exsilium/pxbee-trigger/pxbee/headers/radio_gpios.h

/****************************************************************************
 * Copyright (C) 2012 - 2015 Digi International Inc, All Rights Reserved.
 *
 * This software is provided as instructional material without charge 
 * by Digi International for use by its employees and customers
 * subject to the following terms.
 *
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
 * LIABILITY
 * IN NO EVENT SHALL DIGI INTERNATIONAL BE LIABLE FOR ANY CLAIM, DAMAGES, 
 * OR OTHER LIABILITY, WHETHER IN AN ACTION OF CONTRACT, TORT, OR OTHERWISE, 
 * ARISING FROM, OUT OF, OR IN CONNECTION WITH THE SOFTWARE, OR THE USE 
 * OR OTHER DEALINGS WITH THE SOFTWARE.
 *
 ****************************************************************************/
#ifndef __RADIO_GPIO_H_
#define __RADIO_GPIO_H_

#include <xbee_config.h>

/* Pull-Direction and Pull-Resistor bit shifting for each XPIN according to
 * Datasheet */
#ifdef CONFIG_XBEE_THT

#define shift_xpin_4  (1<<10)
#define shift_xpin_6  (1<<11)
#define shift_xpin_7  (1<<12)
#define shift_xpin_9  (1<<6)
#define shift_xpin_11 (1<<0)
#define shift_xpin_13 (1<<9)
#define shift_xpin_15 (1<<8)
#define shift_xpin_17 (1<<1)
#define shift_xpin_18 (1<<2)
#define shift_xpin_19 (1<<3)
#define shift_xpin_20 (1<<4)

#elif defined (CONFIG_XBEE_SMT)
#define shift_xpin_5  (1<<10)
#define shift_xpin_7  (1<<11)
#define shift_xpin_8  (1<<12)
#define shift_xpin_10 (1<<6)
#define shift_xpin_24 (1<<0)
#define shift_xpin_26 (1<<9)
#define shift_xpin_28 (1<<8)
#define shift_xpin_30 (1<<1)
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
#endif
#ifndef orPR32
#define orPR32 0
#endif
#ifndef andPR32
#define andPR32 ~0
#endif

#ifndef orPD33
#define orPD33 0
#endif
#ifndef andPD33
#define andPD33 ~0
#endif
#ifndef orPR33
#define orPR33 0
#endif
#ifndef andPR33
#define andPR33 ~0
#endif

#endif /* __RADIO_GPIO_H_ */
