exsilium/pxbee-trigger/pxbee/headers/mc9s08qe128.h

/* Based on CPU DB MC9S08QE128_80, version 3.00.066 (RegistersPrg V2.32) */
/*
** ###################################################################
**     Filename  : mc9s08qe128.h
**     Processor : MC9S08QE128CLK
**     FileFormat: V2.32
**     DataSheet : MC9S08QE128RM Rev. 2 6/2007
**     Compiler  : CodeWarrior compiler
**     Date/Time : 5.10.2010, 13:55
**     Abstract  :
**         This header implements the mapping of I/O devices.
**
**     Copyright : 1997 - 2010 Freescale Semiconductor, Inc. All Rights Reserved.
**     
**     http      : www.freescale.com
**     mail      : support@freescale.com
**
**     CPU Registers Revisions:
**               - none
**
**     File-Format-Revisions:
**      - 22.01.2007, V2.12 :
**               - Changes have not affected this file (because they are related to another family)
**      - 01.03.2007, V2.13 :
**               - Flash commands constants values converted to HEX format
**      - 02.03.2007, V2.14 :
**               - Interrupt vector numbers added into .H, see VectorNumber_*
**      - 26.03.2007, V2.15 :
**               - Changes have not affected this file (because they are related to another family)
**      - 10.05.2007, V2.16 :
**               - Fixed flash commands definition for ColdFireV1 assembler (equ -> .equ)
**      - 05.06.2007, V2.17 :
**               - Changes have not affected this file (because they are related to another family)
**      - 19.07.2007, V2.18 :
**               - Improved number of blanked lines inside register structures
**      - 06.08.2007, V2.19 :
**               - CPUDB revisions generated ahead of the file-format revisions.
**      - 11.09.2007, V2.20 :
**               - Added comment about initialization of unbonded pins.
**      - 02.01.2008, V2.21 :
**               - Changes have not affected this file (because they are related to another family)
**      - 13.02.2008, V2.22 :
**               - Changes have not affected this file (because they are related to another family)
**      - 20.02.2008, V2.23 :
**               - Changes have not affected this file (because they are related to another family)
**      - 03.07.2008, V2.24 :
**               - Added support for bits with name starting with number (like "1HZ")
**      - 28.11.2008, V2.25 :
**               - StandBy RAM array declaration for ANSI-C added
**      - 1.12.2008, V2.26 :
**               - Duplication of bit (or bit-group) name with register name is not marked as a problem, if register is internal only and it is not displayed in I/O map.
**      - 17.3.2009, V2.27 :
**               - Merged bit-group is not generated, if the name matches with another bit name in the register
**      - 6.4.2009, V2.28 :
**               - Fixed generation of merged bits for bit-groups with a digit at the end, if group-name is defined in CPUDB
**      - 3.8.2009, V2.29 :
**               - If there is just one bits group matching register name, single bits are not generated
**      - 10.9.2009, V2.30 :
**               - Fixed generation of registers arrays.
**      - 15.10.2009, V2.31 :
**               - HCS08 family: Bits and bit-groups are published for 16-bit registers: 8-bit overlay registers are required.
**      - 18.05.2010, V2.32 :
**               - MISRA compliance: U/UL suffixes added to all numbers (_MASK,_BITNUM and addresses)
**
**     Not all general-purpose I/O pins are available on all packages or on all mask sets of a specific
**     derivative device. To avoid extra current drain from floating input pins, the user’s reset
**     initialization routine in the application program must either enable on-chip pull-up devices
**     or change the direction of unconnected pins to outputs so the pins do not float.
** ###################################################################
*/

#ifndef _MC9S08QE128_H
#define _MC9S08QE128_H

#define FOPT_SEC00_MASK                 1U

/*lint -save  -e950 -esym(960,18.4) -e46 -esym(961,19.7) Disable MISRA rule (1.1,18.4,6.4,19.7) checking. */
/* Types definition */
typedef unsigned char byte;
typedef unsigned int word;
typedef unsigned long dword;
typedef unsigned long dlong[2];

/* Watchdog reset macro */
#ifndef __RESET_WATCHDOG
#ifdef _lint
  #define __RESET_WATCHDOG()  /* empty */
#else
  #define __RESET_WATCHDOG() {asm sta SRS;}
#endif
#endif /* __RESET_WATCHDOG */

#define REG_BASE 0x0000                /* Base address for the I/O register block */


#pragma MESSAGE DISABLE C1106 /* WARNING C1106: Non-standard bitfield type */

/**************** interrupt vector numbers ****************/
#define VectorNumber_Vtpm3ovf           31U
#define VectorNumber_Vtpm3ch5           30U
#define VectorNumber_Vtpm3ch4           29U
#define VectorNumber_Vtpm3ch3           28U
#define VectorNumber_Vtpm3ch2           27U
#define VectorNumber_Vtpm3ch1           26U
#define VectorNumber_Vtpm3ch0           25U
#define VectorNumber_Vrtc               24U
#define VectorNumber_Vsci2tx            23U
#define VectorNumber_Vsci2rx            22U
#define VectorNumber_Vsci2err           21U
#define VectorNumber_Vacmpx             20U
#define VectorNumber_Vadc               19U
#define VectorNumber_Vkeyboard          18U
#define VectorNumber_Viicx              17U
#define VectorNumber_Vsci1tx            16U
#define VectorNumber_Vsci1rx            15U
#define VectorNumber_Vsci1err           14U
#define VectorNumber_Vspi1              13U
#define VectorNumber_Vspi2              12U
#define VectorNumber_Vtpm2ovf           11U
#define VectorNumber_Vtpm2ch2           10U
#define VectorNumber_Vtpm2ch1           9U
#define VectorNumber_Vtpm2ch0           8U
#define VectorNumber_Vtpm1ovf           7U
#define VectorNumber_Vtpm1ch2           6U
#define VectorNumber_Vtpm1ch1           5U
#define VectorNumber_Vtpm1ch0           4U
#define VectorNumber_Vlvd               3U
#define VectorNumber_Virq               2U
#define VectorNumber_Vswi               1U
#define VectorNumber_Vreset             0U

/**************** interrupt vector table ****************/
#define Vtpm3ovf                        0xFFC0U
#define Vtpm3ch5                        0xFFC2U
#define Vtpm3ch4                        0xFFC4U
#define Vtpm3ch3                        0xFFC6U
#define Vtpm3ch2                        0xFFC8U
#define Vtpm3ch1                        0xFFCAU
#define Vtpm3ch0                        0xFFCCU
#define Vrtc                            0xFFCEU
#define Vsci2tx                         0xFFD0U
#define Vsci2rx                         0xFFD2U
#define Vsci2err                        0xFFD4U
#define Vacmpx                          0xFFD6U
#define Vadc                            0xFFD8U
#define Vkeyboard                       0xFFDAU
#define Viicx                           0xFFDCU
#define Vsci1tx                         0xFFDEU
#define Vsci1rx                         0xFFE0U
#define Vsci1err                        0xFFE2U
#define Vspi1                           0xFFE4U
#define Vspi2                           0xFFE6U
#define Vtpm2ovf                        0xFFE8U
#define Vtpm2ch2                        0xFFEAU
#define Vtpm2ch1                        0xFFECU
#define Vtpm2ch0                        0xFFEEU
#define Vtpm1ovf                        0xFFF0U
#define Vtpm1ch2                        0xFFF2U
#define Vtpm1ch1                        0xFFF4U
#define Vtpm1ch0                        0xFFF6U
#define Vlvd                            0xFFF8U
#define Virq                            0xFFFAU
#define Vswi                            0xFFFCU
#define Vreset                          0xFFFEU

/**************** registers I/O map ****************/

/*** PTAD - Port A Data Register; 0x00000000 ***/
typedef union {
  byte Byte;
  struct {
    byte PTAD0       :1;                                       /* Port A Data Register Bit 0 */
    byte PTAD1       :1;                                       /* Port A Data Register Bit 1 */
    byte PTAD2       :1;                                       /* Port A Data Register Bit 2 */
    byte PTAD3       :1;                                       /* Port A Data Register Bit 3 */
    byte PTAD4       :1;                                       /* Port A Data Register Bit 4 */
    byte PTAD5       :1;                                       /* Port A Data Register Bit 5 */
    byte PTAD6       :1;                                       /* Port A Data Register Bit 6 */
    byte PTAD7       :1;                                       /* Port A Data Register Bit 7 */
  } Bits;
} PTADSTR;
extern volatile PTADSTR _PTAD @0x00000000;
#define PTAD                            _PTAD.Byte
#define PTAD_PTAD0                      _PTAD.Bits.PTAD0
#define PTAD_PTAD1                      _PTAD.Bits.PTAD1
#define PTAD_PTAD2                      _PTAD.Bits.PTAD2
#define PTAD_PTAD3                      _PTAD.Bits.PTAD3
#define PTAD_PTAD4                      _PTAD.Bits.PTAD4
#define PTAD_PTAD5                      _PTAD.Bits.PTAD5
#define PTAD_PTAD6                      _PTAD.Bits.PTAD6
#define PTAD_PTAD7                      _PTAD.Bits.PTAD7

#define PTAD_PTAD0_MASK                 1U
#define PTAD_PTAD1_MASK                 2U
#define PTAD_PTAD2_MASK                 4U
#define PTAD_PTAD3_MASK                 8U
#define PTAD_PTAD4_MASK                 16U
#define PTAD_PTAD5_MASK                 32U
#define PTAD_PTAD6_MASK                 64U
#define PTAD_PTAD7_MASK                 128U


/*** PTADD - Port A Data Direction Register; 0x00000001 ***/
typedef union {
  byte Byte;
  struct {
    byte PTADD0      :1;                                       /* Data Direction for Port A Bit 0 */
    byte PTADD1      :1;                                       /* Data Direction for Port A Bit 1 */
    byte PTADD2      :1;                                       /* Data Direction for Port A Bit 2 */
    byte PTADD3      :1;                                       /* Data Direction for Port A Bit 3 */
    byte PTADD4      :1;                                       /* Data Direction for Port A Bit 4 */
    byte PTADD5      :1;                                       /* Data Direction for Port A Bit 5 */
    byte PTADD6      :1;                                       /* Data Direction for Port A Bit 6 */
    byte PTADD7      :1;                                       /* Data Direction for Port A Bit 7 */
  } Bits;
} PTADDSTR;
extern volatile PTADDSTR _PTADD @0x00000001;
#define PTADD                           _PTADD.Byte
#define PTADD_PTADD0                    _PTADD.Bits.PTADD0
#define PTADD_PTADD1                    _PTADD.Bits.PTADD1
#define PTADD_PTADD2                    _PTADD.Bits.PTADD2
#define PTADD_PTADD3                    _PTADD.Bits.PTADD3
#define PTADD_PTADD4                    _PTADD.Bits.PTADD4
#define PTADD_PTADD5                    _PTADD.Bits.PTADD5
#define PTADD_PTADD6                    _PTADD.Bits.PTADD6
#define PTADD_PTADD7                    _PTADD.Bits.PTADD7

#define PTADD_PTADD0_MASK               1U
#define PTADD_PTADD1_MASK               2U
#define PTADD_PTADD2_MASK               4U
#define PTADD_PTADD3_MASK               8U
#define PTADD_PTADD4_MASK               16U
#define PTADD_PTADD5_MASK               32U
#define PTADD_PTADD6_MASK               64U
#define PTADD_PTADD7_MASK               128U


/*** PTBD - Port B Data Register; 0x00000002 ***/
typedef union {
  byte Byte;
  struct {
    byte PTBD0       :1;                                       /* Port B Data Register Bit 0 */
    byte PTBD1       :1;                                       /* Port B Data Register Bit 1 */
    byte PTBD2       :1;                                       /* Port B Data Register Bit 2 */
    byte PTBD3       :1;                                       /* Port B Data Register Bit 3 */
    byte PTBD4       :1;                                       /* Port B Data Register Bit 4 */
    byte PTBD5       :1;                                       /* Port B Data Register Bit 5 */
    byte PTBD6       :1;                                       /* Port B Data Register Bit 6 */
    byte PTBD7       :1;                                       /* Port B Data Register Bit 7 */
  } Bits;
} PTBDSTR;
extern volatile PTBDSTR _PTBD @0x00000002;
#define PTBD                            _PTBD.Byte
#define PTBD_PTBD0                      _PTBD.Bits.PTBD0
#define PTBD_PTBD1                      _PTBD.Bits.PTBD1
#define PTBD_PTBD2                      _PTBD.Bits.PTBD2
#define PTBD_PTBD3                      _PTBD.Bits.PTBD3
#define PTBD_PTBD4                      _PTBD.Bits.PTBD4
#define PTBD_PTBD5                      _PTBD.Bits.PTBD5
#define PTBD_PTBD6                      _PTBD.Bits.PTBD6
#define PTBD_PTBD7                      _PTBD.Bits.PTBD7

#define PTBD_PTBD0_MASK                 1U
#define PTBD_PTBD1_MASK                 2U
#define PTBD_PTBD2_MASK                 4U
#define PTBD_PTBD3_MASK                 8U
#define PTBD_PTBD4_MASK                 16U
#define PTBD_PTBD5_MASK                 32U
#define PTBD_PTBD6_MASK                 64U
#define PTBD_PTBD7_MASK                 128U


/*** PTBDD - Port B Data Direction Register; 0x00000003 ***/
typedef union {
  byte Byte;
  struct {
    byte PTBDD0      :1;                                       /* Data Direction for Port B Bit 0 */
    byte PTBDD1      :1;                                       /* Data Direction for Port B Bit 1 */
    byte PTBDD2      :1;                                       /* Data Direction for Port B Bit 2 */
    byte PTBDD3      :1;                                       /* Data Direction for Port B Bit 3 */
    byte PTBDD4      :1;                                       /* Data Direction for Port B Bit 4 */
    byte PTBDD5      :1;                                       /* Data Direction for Port B Bit 5 */
    byte PTBDD6      :1;                                       /* Data Direction for Port B Bit 6 */
    byte PTBDD7      :1;                                       /* Data Direction for Port B Bit 7 */
  } Bits;
} PTBDDSTR;
extern volatile PTBDDSTR _PTBDD @0x00000003;
#define PTBDD                           _PTBDD.Byte
#define PTBDD_PTBDD0                    _PTBDD.Bits.PTBDD0
#define PTBDD_PTBDD1                    _PTBDD.Bits.PTBDD1
#define PTBDD_PTBDD2                    _PTBDD.Bits.PTBDD2
#define PTBDD_PTBDD3                    _PTBDD.Bits.PTBDD3
#define PTBDD_PTBDD4                    _PTBDD.Bits.PTBDD4
#define PTBDD_PTBDD5                    _PTBDD.Bits.PTBDD5
#define PTBDD_PTBDD6                    _PTBDD.Bits.PTBDD6
#define PTBDD_PTBDD7                    _PTBDD.Bits.PTBDD7

#define PTBDD_PTBDD0_MASK               1U
#define PTBDD_PTBDD1_MASK               2U
#define PTBDD_PTBDD2_MASK               4U
#define PTBDD_PTBDD3_MASK               8U
#define PTBDD_PTBDD4_MASK               16U
#define PTBDD_PTBDD5_MASK               32U
#define PTBDD_PTBDD6_MASK               64U
#define PTBDD_PTBDD7_MASK               128U


/*** PTCD - Port C Data Register; 0x00000004 ***/
typedef union {
  byte Byte;
  struct {
    byte PTCD0       :1;                                       /* Port C Data Register Bit 0 */
    byte PTCD1       :1;                                       /* Port C Data Register Bit 1 */
    byte PTCD2       :1;                                       /* Port C Data Register Bit 2 */
    byte PTCD3       :1;                                       /* Port C Data Register Bit 3 */
    byte PTCD4       :1;                                       /* Port C Data Register Bit 4 */
    byte PTCD5       :1;                                       /* Port C Data Register Bit 5 */
    byte PTCD6       :1;                                       /* Port C Data Register Bit 6 */
    byte PTCD7       :1;                                       /* Port C Data Register Bit 7 */
  } Bits;
} PTCDSTR;
extern volatile PTCDSTR _PTCD @0x00000004;
#define PTCD                            _PTCD.Byte
#define PTCD_PTCD0                      _PTCD.Bits.PTCD0
#define PTCD_PTCD1                      _PTCD.Bits.PTCD1
#define PTCD_PTCD2                      _PTCD.Bits.PTCD2
#define PTCD_PTCD3                      _PTCD.Bits.PTCD3
#define PTCD_PTCD4                      _PTCD.Bits.PTCD4
#define PTCD_PTCD5                      _PTCD.Bits.PTCD5
#define PTCD_PTCD6                      _PTCD.Bits.PTCD6
#define PTCD_PTCD7                      _PTCD.Bits.PTCD7

#define PTCD_PTCD0_MASK                 1U
#define PTCD_PTCD1_MASK                 2U
#define PTCD_PTCD2_MASK                 4U
#define PTCD_PTCD3_MASK                 8U
#define PTCD_PTCD4_MASK                 16U
#define PTCD_PTCD5_MASK                 32U
#define PTCD_PTCD6_MASK                 64U
#define PTCD_PTCD7_MASK                 128U


/*** PTCDD - Port C Data Direction Register; 0x00000005 ***/
typedef union {
  byte Byte;
  struct {
    byte PTCDD0      :1;                                       /* Data Direction for Port C Bit 0 */
    byte PTCDD1      :1;                                       /* Data Direction for Port C Bit 1 */
    byte PTCDD2      :1;                                       /* Data Direction for Port C Bit 2 */
    byte PTCDD3      :1;                                       /* Data Direction for Port C Bit 3 */
    byte PTCDD4      :1;                                       /* Data Direction for Port C Bit 4 */
    byte PTCDD5      :1;                                       /* Data Direction for Port C Bit 5 */
    byte PTCDD6      :1;                                       /* Data Direction for Port C Bit 6 */
    byte PTCDD7      :1;                                       /* Data Direction for Port C Bit 7 */
  } Bits;
} PTCDDSTR;
extern volatile PTCDDSTR _PTCDD @0x00000005;
#define PTCDD                           _PTCDD.Byte
#define PTCDD_PTCDD0                    _PTCDD.Bits.PTCDD0
#define PTCDD_PTCDD1                    _PTCDD.Bits.PTCDD1
#define PTCDD_PTCDD2                    _PTCDD.Bits.PTCDD2
#define PTCDD_PTCDD3                    _PTCDD.Bits.PTCDD3
#define PTCDD_PTCDD4                    _PTCDD.Bits.PTCDD4
#define PTCDD_PTCDD5                    _PTCDD.Bits.PTCDD5
#define PTCDD_PTCDD6                    _PTCDD.Bits.PTCDD6
#define PTCDD_PTCDD7                    _PTCDD.Bits.PTCDD7

#define PTCDD_PTCDD0_MASK               1U
#define PTCDD_PTCDD1_MASK               2U
#define PTCDD_PTCDD2_MASK               4U
#define PTCDD_PTCDD3_MASK               8U
#define PTCDD_PTCDD4_MASK               16U
#define PTCDD_PTCDD5_MASK               32U
#define PTCDD_PTCDD6_MASK               64U
#define PTCDD_PTCDD7_MASK               128U


/*** PTDD - Port D Data Register; 0x00000006 ***/
typedef union {
  byte Byte;
  struct {
    byte PTDD0       :1;                                       /* Port D Data Register Bit 0 */
    byte PTDD1       :1;                                       /* Port D Data Register Bit 1 */
    byte PTDD2       :1;                                       /* Port D Data Register Bit 2 */
    byte PTDD3       :1;                                       /* Port D Data Register Bit 3 */
    byte PTDD4       :1;                                       /* Port D Data Register Bit 4 */
    byte PTDD5       :1;                                       /* Port D Data Register Bit 5 */
    byte PTDD6       :1;                                       /* Port D Data Register Bit 6 */
    byte PTDD7       :1;                                       /* Port D Data Register Bit 7 */
  } Bits;
} PTDDSTR;
extern volatile PTDDSTR _PTDD @0x00000006;
#define PTDD                            _PTDD.Byte
#define PTDD_PTDD0                      _PTDD.Bits.PTDD0
#define PTDD_PTDD1                      _PTDD.Bits.PTDD1
#define PTDD_PTDD2                      _PTDD.Bits.PTDD2
#define PTDD_PTDD3                      _PTDD.Bits.PTDD3
#define PTDD_PTDD4                      _PTDD.Bits.PTDD4
#define PTDD_PTDD5                      _PTDD.Bits.PTDD5
#define PTDD_PTDD6                      _PTDD.Bits.PTDD6
#define PTDD_PTDD7                      _PTDD.Bits.PTDD7

#define PTDD_PTDD0_MASK                 1U
#define PTDD_PTDD1_MASK                 2U
#define PTDD_PTDD2_MASK                 4U
#define PTDD_PTDD3_MASK                 8U
#define PTDD_PTDD4_MASK                 16U
#define PTDD_PTDD5_MASK                 32U
#define PTDD_PTDD6_MASK                 64U
#define PTDD_PTDD7_MASK                 128U


/*** PTDDD - Port D Data Direction Register; 0x00000007 ***/
typedef union {
  byte Byte;
  struct {
    byte PTDDD0      :1;                                       /* Data Direction for Port D Bit 0 */
    byte PTDDD1      :1;                                       /* Data Direction for Port D Bit 1 */
    byte PTDDD2      :1;                                       /* Data Direction for Port D Bit 2 */
    byte PTDDD3      :1;                                       /* Data Direction for Port D Bit 3 */
    byte PTDDD4      :1;                                       /* Data Direction for Port D Bit 4 */
    byte PTDDD5      :1;                                       /* Data Direction for Port D Bit 5 */
    byte PTDDD6      :1;                                       /* Data Direction for Port D Bit 6 */
    byte PTDDD7      :1;                                       /* Data Direction for Port D Bit 7 */
  } Bits;
} PTDDDSTR;
extern volatile PTDDDSTR _PTDDD @0x00000007;
#define PTDDD                           _PTDDD.Byte
#define PTDDD_PTDDD0                    _PTDDD.Bits.PTDDD0
#define PTDDD_PTDDD1                    _PTDDD.Bits.PTDDD1
#define PTDDD_PTDDD2                    _PTDDD.Bits.PTDDD2
#define PTDDD_PTDDD3                    _PTDDD.Bits.PTDDD3
#define PTDDD_PTDDD4                    _PTDDD.Bits.PTDDD4
#define PTDDD_PTDDD5                    _PTDDD.Bits.PTDDD5
#define PTDDD_PTDDD6                    _PTDDD.Bits.PTDDD6
#define PTDDD_PTDDD7                    _PTDDD.Bits.PTDDD7

#define PTDDD_PTDDD0_MASK               1U
#define PTDDD_PTDDD1_MASK               2U
#define PTDDD_PTDDD2_MASK               4U
#define PTDDD_PTDDD3_MASK               8U
#define PTDDD_PTDDD4_MASK               16U
#define PTDDD_PTDDD5_MASK               32U
#define PTDDD_PTDDD6_MASK               64U
#define PTDDD_PTDDD7_MASK               128U


/*** PTED - Port E Data Register; 0x00000008 ***/
typedef union {
  byte Byte;
  struct {
    byte PTED0       :1;                                       /* Port E Data Register Bit 0 */
    byte PTED1       :1;                                       /* Port E Data Register Bit 1 */
    byte PTED2       :1;                                       /* Port E Data Register Bit 2 */
    byte PTED3       :1;                                       /* Port E Data Register Bit 3 */
    byte PTED4       :1;                                       /* Port E Data Register Bit 4 */
    byte PTED5       :1;                                       /* Port E Data Register Bit 5 */
    byte PTED6       :1;                                       /* Port E Data Register Bit 6 */
    byte PTED7       :1;                                       /* Port E Data Register Bit 7 */
  } Bits;
} PTEDSTR;
extern volatile PTEDSTR _PTED @0x00000008;
#define PTED                            _PTED.Byte
#define PTED_PTED0                      _PTED.Bits.PTED0
#define PTED_PTED1                      _PTED.Bits.PTED1
#define PTED_PTED2                      _PTED.Bits.PTED2
#define PTED_PTED3                      _PTED.Bits.PTED3
#define PTED_PTED4                      _PTED.Bits.PTED4
#define PTED_PTED5                      _PTED.Bits.PTED5
#define PTED_PTED6                      _PTED.Bits.PTED6
#define PTED_PTED7                      _PTED.Bits.PTED7

#define PTED_PTED0_MASK                 1U
#define PTED_PTED1_MASK                 2U
#define PTED_PTED2_MASK                 4U
#define PTED_PTED3_MASK                 8U
#define PTED_PTED4_MASK                 16U
#define PTED_PTED5_MASK                 32U
#define PTED_PTED6_MASK                 64U
#define PTED_PTED7_MASK                 128U


/*** PTEDD - Port E Data Direction Register; 0x00000009 ***/
typedef union {
  byte Byte;
  struct {
    byte PTEDD0      :1;                                       /* Data Direction for Port E Bit 0 */
    byte PTEDD1      :1;                                       /* Data Direction for Port E Bit 1 */
    byte PTEDD2      :1;                                       /* Data Direction for Port E Bit 2 */
    byte PTEDD3      :1;                                       /* Data Direction for Port E Bit 3 */
    byte PTEDD4      :1;                                       /* Data Direction for Port E Bit 4 */
    byte PTEDD5      :1;                                       /* Data Direction for Port E Bit 5 */
    byte PTEDD6      :1;                                       /* Data Direction for Port E Bit 6 */
    byte PTEDD7      :1;                                       /* Data Direction for Port E Bit 7 */
  } Bits;
} PTEDDSTR;
extern volatile PTEDDSTR _PTEDD @0x00000009;
#define PTEDD                           _PTEDD.Byte
#define PTEDD_PTEDD0                    _PTEDD.Bits.PTEDD0
#define PTEDD_PTEDD1                    _PTEDD.Bits.PTEDD1
#define PTEDD_PTEDD2                    _PTEDD.Bits.PTEDD2
#define PTEDD_PTEDD3                    _PTEDD.Bits.PTEDD3
#define PTEDD_PTEDD4                    _PTEDD.Bits.PTEDD4
#define PTEDD_PTEDD5                    _PTEDD.Bits.PTEDD5
#define PTEDD_PTEDD6                    _PTEDD.Bits.PTEDD6
#define PTEDD_PTEDD7                    _PTEDD.Bits.PTEDD7

#define PTEDD_PTEDD0_MASK               1U
#define PTEDD_PTEDD1_MASK               2U
#define PTEDD_PTEDD2_MASK               4U
#define PTEDD_PTEDD3_MASK               8U
#define PTEDD_PTEDD4_MASK               16U
#define PTEDD_PTEDD5_MASK               32U
#define PTEDD_PTEDD6_MASK               64U
#define PTEDD_PTEDD7_MASK               128U


/*** PTFD - Port F Data Register; 0x0000000A ***/
typedef union {
  byte Byte;
  struct {
    byte PTFD0       :1;                                       /* Port F Data Register Bit 0 */
    byte PTFD1       :1;                                       /* Port F Data Register Bit 1 */
    byte PTFD2       :1;                                       /* Port F Data Register Bit 2 */
    byte PTFD3       :1;                                       /* Port F Data Register Bit 3 */
    byte PTFD4       :1;                                       /* Port F Data Register Bit 4 */
    byte PTFD5       :1;                                       /* Port F Data Register Bit 5 */
    byte PTFD6       :1;                                       /* Port F Data Register Bit 6 */
    byte PTFD7       :1;                                       /* Port F Data Register Bit 7 */
  } Bits;
} PTFDSTR;
extern volatile PTFDSTR _PTFD @0x0000000A;
#define PTFD                            _PTFD.Byte
#define PTFD_PTFD0                      _PTFD.Bits.PTFD0
#define PTFD_PTFD1                      _PTFD.Bits.PTFD1
#define PTFD_PTFD2                      _PTFD.Bits.PTFD2
#define PTFD_PTFD3                      _PTFD.Bits.PTFD3
#define PTFD_PTFD4                      _PTFD.Bits.PTFD4
#define PTFD_PTFD5                      _PTFD.Bits.PTFD5
#define PTFD_PTFD6                      _PTFD.Bits.PTFD6
#define PTFD_PTFD7                      _PTFD.Bits.PTFD7

#define PTFD_PTFD0_MASK                 1U
#define PTFD_PTFD1_MASK                 2U
#define PTFD_PTFD2_MASK                 4U
#define PTFD_PTFD3_MASK                 8U
#define PTFD_PTFD4_MASK                 16U
#define PTFD_PTFD5_MASK                 32U
#define PTFD_PTFD6_MASK                 64U
#define PTFD_PTFD7_MASK                 128U


/*** PTFDD - Port F Data Direction Register; 0x0000000B ***/
typedef union {
  byte Byte;
  struct {
    byte PTFDD0      :1;                                       /* Data Direction for Port F Bit 0 */
    byte PTFDD1      :1;                                       /* Data Direction for Port F Bit 1 */
    byte PTFDD2      :1;                                       /* Data Direction for Port F Bit 2 */
    byte PTFDD3      :1;                                       /* Data Direction for Port F Bit 3 */
    byte PTFDD4      :1;                                       /* Data Direction for Port F Bit 4 */
    byte PTFDD5      :1;                                       /* Data Direction for Port F Bit 5 */
    byte PTFDD6      :1;                                       /* Data Direction for Port F Bit 6 */
    byte PTFDD7      :1;                                       /* Data Direction for Port F Bit 7 */
  } Bits;
} PTFDDSTR;
extern volatile PTFDDSTR _PTFDD @0x0000000B;
#define PTFDD                           _PTFDD.Byte
#define PTFDD_PTFDD0                    _PTFDD.Bits.PTFDD0
#define PTFDD_PTFDD1                    _PTFDD.Bits.PTFDD1
#define PTFDD_PTFDD2                    _PTFDD.Bits.PTFDD2
#define PTFDD_PTFDD3                    _PTFDD.Bits.PTFDD3
#define PTFDD_PTFDD4                    _PTFDD.Bits.PTFDD4
#define PTFDD_PTFDD5                    _PTFDD.Bits.PTFDD5
#define PTFDD_PTFDD6                    _PTFDD.Bits.PTFDD6
#define PTFDD_PTFDD7                    _PTFDD.Bits.PTFDD7

#define PTFDD_PTFDD0_MASK               1U
#define PTFDD_PTFDD1_MASK               2U
#define PTFDD_PTFDD2_MASK               4U
#define PTFDD_PTFDD3_MASK               8U
#define PTFDD_PTFDD4_MASK               16U
#define PTFDD_PTFDD5_MASK               32U
#define PTFDD_PTFDD6_MASK               64U
#define PTFDD_PTFDD7_MASK               128U


/*** KBI1SC - KBI1 Status and Control Register; 0x0000000C ***/
typedef union {
  byte Byte;
  struct {
    byte KBIMOD      :1;                                       /* Keyboard Detection Mode */
    byte KBIE        :1;                                       /* Keyboard Interrupt Enable */
    byte KBACK       :1;                                       /* Keyboard Interrupt Acknowledge */
    byte KBF         :1;                                       /* Keyboard Interrupt Flag */
    byte             :1; 
    byte             :1; 
    byte             :1; 
    byte             :1; 
  } Bits;
} KBI1SCSTR;
extern volatile KBI1SCSTR _KBI1SC @0x0000000C;
#define KBI1SC                          _KBI1SC.Byte
#define KBI1SC_KBIMOD                   _KBI1SC.Bits.KBIMOD
#define KBI1SC_KBIE                     _KBI1SC.Bits.KBIE
#define KBI1SC_KBACK                    _KBI1SC.Bits.KBACK
#define KBI1SC_KBF                      _KBI1SC.Bits.KBF

#define KBI1SC_KBIMOD_MASK              1U
#define KBI1SC_KBIE_MASK                2U
#define KBI1SC_KBACK_MASK               4U
#define KBI1SC_KBF_MASK                 8U


/*** KBI1PE - KBI1 Pin Enable Register; 0x0000000D ***/
typedef union {
  byte Byte;
  struct {
    byte KBIPE0      :1;                                       /* Keyboard Pin Enable for KBI Port Bit 0 */
    byte KBIPE1      :1;                                       /* Keyboard Pin Enable for KBI Port Bit 1 */
    byte KBIPE2      :1;                                       /* Keyboard Pin Enable for KBI Port Bit 2 */
    byte KBIPE3      :1;                                       /* Keyboard Pin Enable for KBI Port Bit 3 */
    byte KBIPE4      :1;                                       /* Keyboard Pin Enable for KBI Port Bit 4 */
    byte KBIPE5      :1;                                       /* Keyboard Pin Enable for KBI Port Bit 5 */
    byte KBIPE6      :1;                                       /* Keyboard Pin Enable for KBI Port Bit 6 */
    byte KBIPE7      :1;                                       /* Keyboard Pin Enable for KBI Port Bit 7 */
  } Bits;
} KBI1PESTR;
extern volatile KBI1PESTR _KBI1PE @0x0000000D;
#define KBI1PE                          _KBI1PE.Byte
#define KBI1PE_KBIPE0                   _KBI1PE.Bits.KBIPE0
#define KBI1PE_KBIPE1                   _KBI1PE.Bits.KBIPE1
#define KBI1PE_KBIPE2                   _KBI1PE.Bits.KBIPE2
#define KBI1PE_KBIPE3                   _KBI1PE.Bits.KBIPE3
#define KBI1PE_KBIPE4                   _KBI1PE.Bits.KBIPE4
#define KBI1PE_KBIPE5                   _KBI1PE.Bits.KBIPE5
#define KBI1PE_KBIPE6                   _KBI1PE.Bits.KBIPE6
#define KBI1PE_KBIPE7                   _KBI1PE.Bits.KBIPE7

#define KBI1PE_KBIPE0_MASK              1U
#define KBI1PE_KBIPE1_MASK              2U
#define KBI1PE_KBIPE2_MASK              4U
#define KBI1PE_KBIPE3_MASK              8U
#define KBI1PE_KBIPE4_MASK              16U
#define KBI1PE_KBIPE5_MASK              32U
#define KBI1PE_KBIPE6_MASK              64U
#define KBI1PE_KBIPE7_MASK              128U


/*** KBI1ES - KBI1 Edge Select Register; 0x0000000E ***/
typedef union {
  byte Byte;
  struct {
    byte KBEDG0      :1;                                       /* Keyboard Edge Select Bit 0 */
    byte KBEDG1      :1;                                       /* Keyboard Edge Select Bit 1 */
    byte KBEDG2      :1;                                       /* Keyboard Edge Select Bit 2 */
    byte KBEDG3      :1;                                       /* Keyboard Edge Select Bit 3 */
    byte KBEDG4      :1;                                       /* Keyboard Edge Select Bit 4 */
    byte KBEDG5      :1;                                       /* Keyboard Edge Select Bit 5 */
    byte KBEDG6      :1;                                       /* Keyboard Edge Select Bit 6 */
    byte KBEDG7      :1;                                       /* Keyboard Edge Select Bit 7 */
  } Bits;
} KBI1ESSTR;
extern volatile KBI1ESSTR _KBI1ES @0x0000000E;
#define KBI1ES                          _KBI1ES.Byte
#define KBI1ES_KBEDG0                   _KBI1ES.Bits.KBEDG0
#define KBI1ES_KBEDG1                   _KBI1ES.Bits.KBEDG1
#define KBI1ES_KBEDG2                   _KBI1ES.Bits.KBEDG2
#define KBI1ES_KBEDG3                   _KBI1ES.Bits.KBEDG3
#define KBI1ES_KBEDG4                   _KBI1ES.Bits.KBEDG4
#define KBI1ES_KBEDG5                   _KBI1ES.Bits.KBEDG5
#define KBI1ES_KBEDG6                   _KBI1ES.Bits.KBEDG6
#define KBI1ES_KBEDG7                   _KBI1ES.Bits.KBEDG7

#define KBI1ES_KBEDG0_MASK              1U
#define KBI1ES_KBEDG1_MASK              2U
#define KBI1ES_KBEDG2_MASK              4U
#define KBI1ES_KBEDG3_MASK              8U
#define KBI1ES_KBEDG4_MASK              16U
#define KBI1ES_KBEDG5_MASK              32U
#define KBI1ES_KBEDG6_MASK              64U
#define KBI1ES_KBEDG7_MASK              128U


/*** IRQSC - Interrupt request status and control register; 0x0000000F ***/
typedef union {
  byte Byte;
  struct {
    byte IRQMOD      :1;                                       /* IRQ Detection Mode */
    byte IRQIE       :1;                                       /* IRQ Interrupt Enable */
    byte IRQACK      :1;                                       /* IRQ Acknowledge */
    byte IRQF        :1;                                       /* IRQ Flag */
    byte IRQPE       :1;                                       /* IRQ Pin Enable */
    byte IRQEDG      :1;                                       /* IRQ Edge Select */
    byte IRQPDD      :1;                                       /* IRQ Pull Device Disable */
    byte             :1; 
  } Bits;
} IRQSCSTR;
extern volatile IRQSCSTR _IRQSC @0x0000000F;
#define IRQSC                           _IRQSC.Byte
#define IRQSC_IRQMOD                    _IRQSC.Bits.IRQMOD
#define IRQSC_IRQIE                     _IRQSC.Bits.IRQIE
#define IRQSC_IRQACK                    _IRQSC.Bits.IRQACK
#define IRQSC_IRQF                      _IRQSC.Bits.IRQF
#define IRQSC_IRQPE                     _IRQSC.Bits.IRQPE
#define IRQSC_IRQEDG                    _IRQSC.Bits.IRQEDG
#define IRQSC_IRQPDD                    _IRQSC.Bits.IRQPDD

#define IRQSC_IRQMOD_MASK               1U
#define IRQSC_IRQIE_MASK                2U
#define IRQSC_IRQACK_MASK               4U
#define IRQSC_IRQF_MASK                 8U
#define IRQSC_IRQPE_MASK                16U
#define IRQSC_IRQEDG_MASK               32U
#define IRQSC_IRQPDD_MASK               64U


/*** ADCSC1 - Status and Control Register 1; 0x00000010 ***/
typedef union {
  byte Byte;
  struct {
    byte ADCH0       :1;                                       /* Input Channel Select Bit 0 */
    byte ADCH1       :1;                                       /* Input Channel Select Bit 1 */
    byte ADCH2       :1;                                       /* Input Channel Select Bit 2 */
    byte ADCH3       :1;                                       /* Input Channel Select Bit 3 */
    byte ADCH4       :1;                                       /* Input Channel Select Bit 4 */
    byte ADCO        :1;                                       /* Continuous Conversion Enable - ADCO is used to enable continuous conversions */
    byte AIEN        :1;                                       /* Interrupt Enable - AIEN is used to enable conversion complete interrupts. When COCO becomes set while AIEN is high, an interrupt is asserted */
    byte COCO        :1;                                       /* Conversion Complete Flag */
  } Bits;
  struct {
    byte grpADCH :5;
    byte         :1;
    byte         :1;
    byte         :1;
  } MergedBits;
} ADCSC1STR;
extern volatile ADCSC1STR _ADCSC1 @0x00000010;
#define ADCSC1                          _ADCSC1.Byte
#define ADCSC1_ADCH0                    _ADCSC1.Bits.ADCH0
#define ADCSC1_ADCH1                    _ADCSC1.Bits.ADCH1
#define ADCSC1_ADCH2                    _ADCSC1.Bits.ADCH2
#define ADCSC1_ADCH3                    _ADCSC1.Bits.ADCH3
#define ADCSC1_ADCH4                    _ADCSC1.Bits.ADCH4
#define ADCSC1_ADCO                     _ADCSC1.Bits.ADCO
#define ADCSC1_AIEN                     _ADCSC1.Bits.AIEN
#define ADCSC1_COCO                     _ADCSC1.Bits.COCO
#define ADCSC1_ADCH                     _ADCSC1.MergedBits.grpADCH

#define ADCSC1_ADCH0_MASK               1U
#define ADCSC1_ADCH1_MASK               2U
#define ADCSC1_ADCH2_MASK               4U
#define ADCSC1_ADCH3_MASK               8U
#define ADCSC1_ADCH4_MASK               16U
#define ADCSC1_ADCO_MASK                32U
#define ADCSC1_AIEN_MASK                64U
#define ADCSC1_COCO_MASK                128U
#define ADCSC1_ADCH_MASK                31U
#define ADCSC1_ADCH_BITNUM              0U


/*** ADCSC2 - Status and Control Register 2; 0x00000011 ***/
typedef union {
  byte Byte;
  struct {
    byte             :1; 
    byte             :1; 
    byte             :1; 
    byte             :1; 
    byte ACFGT       :1;                                       /* Compare Function Greater Than Enable */
    byte ACFE        :1;                                       /* Compare Function Enable - ACFE is used to enable the compare function */
    byte ADTRG       :1;                                       /* Conversion Trigger Select-ADTRG is used to select the type of trigger to be used for initiating a conversion */
    byte ADACT       :1;                                       /* Conversion Active - ADACT indicates that a conversion is in progress. ADACT is set when a conversion is initiated and cleared when a conversion is completed or aborted */
  } Bits;
} ADCSC2STR;
extern volatile ADCSC2STR _ADCSC2 @0x00000011;
#define ADCSC2                          _ADCSC2.Byte
#define ADCSC2_ACFGT                    _ADCSC2.Bits.ACFGT
#define ADCSC2_ACFE                     _ADCSC2.Bits.ACFE
#define ADCSC2_ADTRG                    _ADCSC2.Bits.ADTRG
#define ADCSC2_ADACT                    _ADCSC2.Bits.ADACT

#define ADCSC2_ACFGT_MASK               16U
#define ADCSC2_ACFE_MASK                32U
#define ADCSC2_ADTRG_MASK               64U
#define ADCSC2_ADACT_MASK               128U


/*** ADCR - Data Result Register; 0x00000012 ***/
typedef union {
  word Word;
   /* Overlapped registers: */
  struct {
    /*** ADCRH - Data Result High Register; 0x00000012 ***/
    union {
      byte Byte;
      struct {
        byte ADR8        :1;                                       /* ADC Result Data Bit 8 */
        byte ADR9        :1;                                       /* ADC Result Data Bit 9 */
        byte ADR10       :1;                                       /* ADC Result Data Bit 10 */
        byte ADR11       :1;                                       /* ADC Result Data Bit 11 */
        byte             :1; 
        byte             :1; 
        byte             :1; 
        byte             :1; 
      } Bits;
      struct {
        byte grpADR_8 :4;
        byte     :1;
        byte     :1;
        byte     :1;
        byte     :1;
      } MergedBits;
    } ADCRHSTR;
    #define ADCRH                       _ADCR.Overlap_STR.ADCRHSTR.Byte
    #define ADCRH_ADR8                  _ADCR.Overlap_STR.ADCRHSTR.Bits.ADR8
    #define ADCRH_ADR9                  _ADCR.Overlap_STR.ADCRHSTR.Bits.ADR9
    #define ADCRH_ADR10                 _ADCR.Overlap_STR.ADCRHSTR.Bits.ADR10
    #define ADCRH_ADR11                 _ADCR.Overlap_STR.ADCRHSTR.Bits.ADR11
    #define ADCRH_ADR_8                 _ADCR.Overlap_STR.ADCRHSTR.MergedBits.grpADR_8
    #define ADCRH_ADR                   ADCRH_ADR_8
    
    #define ADCRH_ADR8_MASK             1U
    #define ADCRH_ADR9_MASK             2U
    #define ADCRH_ADR10_MASK            4U
    #define ADCRH_ADR11_MASK            8U
    #define ADCRH_ADR_8_MASK            15U
    #define ADCRH_ADR_8_BITNUM          0U
    

    /*** ADCRL - Data Result Low Register; 0x00000013 ***/
    union {
      byte Byte;
      struct {
        byte ADR0        :1;                                       /* ADC Result Data Bit 0 */
        byte ADR1        :1;                                       /* ADC Result Data Bit 1 */
        byte ADR2        :1;                                       /* ADC Result Data Bit 2 */
        byte ADR3        :1;                                       /* ADC Result Data Bit 3 */
        byte ADR4        :1;                                       /* ADC Result Data Bit 4 */
        byte ADR5        :1;                                       /* ADC Result Data Bit 5 */
        byte ADR6        :1;                                       /* ADC Result Data Bit 6 */
        byte ADR7        :1;                                       /* ADC Result Data Bit 7 */
      } Bits;
    } ADCRLSTR;
    #define ADCRL                       _ADCR.Overlap_STR.ADCRLSTR.Byte
    #define ADCRL_ADR0                  _ADCR.Overlap_STR.ADCRLSTR.Bits.ADR0
    #define ADCRL_ADR1                  _ADCR.Overlap_STR.ADCRLSTR.Bits.ADR1
    #define ADCRL_ADR2                  _ADCR.Overlap_STR.ADCRLSTR.Bits.ADR2
    #define ADCRL_ADR3                  _ADCR.Overlap_STR.ADCRLSTR.Bits.ADR3
    #define ADCRL_ADR4                  _ADCR.Overlap_STR.ADCRLSTR.Bits.ADR4
    #define ADCRL_ADR5                  _ADCR.Overlap_STR.ADCRLSTR.Bits.ADR5
    #define ADCRL_ADR6                  _ADCR.Overlap_STR.ADCRLSTR.Bits.ADR6
    #define ADCRL_ADR7                  _ADCR.Overlap_STR.ADCRLSTR.Bits.ADR7
    
    #define ADCRL_ADR0_MASK             1U
    #define ADCRL_ADR1_MASK             2U
    #define ADCRL_ADR2_MASK             4U
    #define ADCRL_ADR3_MASK             8U
    #define ADCRL_ADR4_MASK             16U
    #define ADCRL_ADR5_MASK             32U
    #define ADCRL_ADR6_MASK             64U
    #define ADCRL_ADR7_MASK             128U
    
  } Overlap_STR;

} ADCRSTR;
extern volatile ADCRSTR _ADCR @0x00000012;
#define ADCR                            _ADCR.Word


/*** ADCCV - Compare Value Register; 0x00000014 ***/
typedef union {
  word Word;
   /* Overlapped registers: */
  struct {
    /*** ADCCVH - Compare Value High Register; 0x00000014 ***/
    union {
      byte Byte;
      struct {
        byte ADCV8       :1;                                       /* Compare Function Value 8 */
        byte ADCV9       :1;                                       /* Compare Function Value 9 */
        byte ADCV10      :1;                                       /* Compare Function Value 10 */
        byte ADCV11      :1;                                       /* Compare Function Value 11 */
        byte             :1; 
        byte             :1; 
        byte             :1; 
        byte             :1; 
      } Bits;
      struct {
        byte grpADCV_8 :4;
        byte     :1;
        byte     :1;
        byte     :1;
        byte     :1;
      } MergedBits;
    } ADCCVHSTR;
    #define ADCCVH                      _ADCCV.Overlap_STR.ADCCVHSTR.Byte
    #define ADCCVH_ADCV8                _ADCCV.Overlap_STR.ADCCVHSTR.Bits.ADCV8
    #define ADCCVH_ADCV9                _ADCCV.Overlap_STR.ADCCVHSTR.Bits.ADCV9
    #define ADCCVH_ADCV10               _ADCCV.Overlap_STR.ADCCVHSTR.Bits.ADCV10
    #define ADCCVH_ADCV11               _ADCCV.Overlap_STR.ADCCVHSTR.Bits.ADCV11
    #define ADCCVH_ADCV_8               _ADCCV.Overlap_STR.ADCCVHSTR.MergedBits.grpADCV_8
    #define ADCCVH_ADCV                 ADCCVH_ADCV_8
    
    #define ADCCVH_ADCV8_MASK           1U
    #define ADCCVH_ADCV9_MASK           2U
    #define ADCCVH_ADCV10_MASK          4U
    #define ADCCVH_ADCV11_MASK          8U
    #define ADCCVH_ADCV_8_MASK          15U
    #define ADCCVH_ADCV_8_BITNUM        0U
    

    /*** ADCCVL - Compare Value Low Register; 0x00000015 ***/
    union {
      byte Byte;
      struct {
        byte ADCV0       :1;                                       /* Compare Function Value 0 */
        byte ADCV1       :1;                                       /* Compare Function Value 1 */
        byte ADCV2       :1;                                       /* Compare Function Value 2 */
        byte ADCV3       :1;                                       /* Compare Function Value 3 */
        byte ADCV4       :1;                                       /* Compare Function Value 4 */
        byte ADCV5       :1;                                       /* Compare Function Value 5 */
        byte ADCV6       :1;                                       /* Compare Function Value 6 */
        byte ADCV7       :1;                                       /* Compare Function Value 7 */
      } Bits;
    } ADCCVLSTR;
    #define ADCCVL                      _ADCCV.Overlap_STR.ADCCVLSTR.Byte
    #define ADCCVL_ADCV0                _ADCCV.Overlap_STR.ADCCVLSTR.Bits.ADCV0
    #define ADCCVL_ADCV1                _ADCCV.Overlap_STR.ADCCVLSTR.Bits.ADCV1
    #define ADCCVL_ADCV2                _ADCCV.Overlap_STR.ADCCVLSTR.Bits.ADCV2
    #define ADCCVL_ADCV3                _ADCCV.Overlap_STR.ADCCVLSTR.Bits.ADCV3
    #define ADCCVL_ADCV4                _ADCCV.Overlap_STR.ADCCVLSTR.Bits.ADCV4
    #define ADCCVL_ADCV5                _ADCCV.Overlap_STR.ADCCVLSTR.Bits.ADCV5
    #define ADCCVL_ADCV6                _ADCCV.Overlap_STR.ADCCVLSTR.Bits.ADCV6
    #define ADCCVL_ADCV7                _ADCCV.Overlap_STR.ADCCVLSTR.Bits.ADCV7
    
    #define ADCCVL_ADCV0_MASK           1U
    #define ADCCVL_ADCV1_MASK           2U
    #define ADCCVL_ADCV2_MASK           4U
    #define ADCCVL_ADCV3_MASK           8U
    #define ADCCVL_ADCV4_MASK           16U
    #define ADCCVL_ADCV5_MASK           32U
    #define ADCCVL_ADCV6_MASK           64U
    #define ADCCVL_ADCV7_MASK           128U
    
  } Overlap_STR;

} ADCCVSTR;
extern volatile ADCCVSTR _ADCCV @0x00000014;
#define ADCCV                           _ADCCV.Word


/*** ADCCFG - Configuration Register; 0x00000016 ***/
typedef union {
  byte Byte;
  struct {
    byte ADICLK0     :1;                                       /* Input Clock Select Bit 0 */
    byte ADICLK1     :1;                                       /* Input Clock Select Bit 1 */
    byte MODE0       :1;                                       /* Conversion Mode Selection Bit 0 */
    byte MODE1       :1;                                       /* Conversion Mode Selection Bit 1 */
    byte ADLSMP      :1;                                       /* Long Sample Time Configuration */
    byte ADIV0       :1;                                       /* Clock Divide Select Bit 0 */
    byte ADIV1       :1;                                       /* Clock Divide Select Bit 1 */
    byte ADLPC       :1;                                       /* Low Power Configuration */
  } Bits;
  struct {
    byte grpADICLK :2;
    byte grpMODE :2;
    byte         :1;
    byte grpADIV :2;
    byte         :1;
  } MergedBits;
} ADCCFGSTR;
extern volatile ADCCFGSTR _ADCCFG @0x00000016;
#define ADCCFG                          _ADCCFG.Byte
#define ADCCFG_ADICLK0                  _ADCCFG.Bits.ADICLK0
#define ADCCFG_ADICLK1                  _ADCCFG.Bits.ADICLK1
#define ADCCFG_MODE0                    _ADCCFG.Bits.MODE0
#define ADCCFG_MODE1                    _ADCCFG.Bits.MODE1
#define ADCCFG_ADLSMP                   _ADCCFG.Bits.ADLSMP
#define ADCCFG_ADIV0                    _ADCCFG.Bits.ADIV0
#define ADCCFG_ADIV1                    _ADCCFG.Bits.ADIV1
#define ADCCFG_ADLPC                    _ADCCFG.Bits.ADLPC
#define ADCCFG_ADICLK                   _ADCCFG.MergedBits.grpADICLK
#define ADCCFG_MODE                     _ADCCFG.MergedBits.grpMODE
#define ADCCFG_ADIV                     _ADCCFG.MergedBits.grpADIV

#define ADCCFG_ADICLK0_MASK             1U
#define ADCCFG_ADICLK1_MASK             2U
#define ADCCFG_MODE0_MASK               4U
#define ADCCFG_MODE1_MASK               8U
#define ADCCFG_ADLSMP_MASK              16U
#define ADCCFG_ADIV0_MASK               32U
#define ADCCFG_ADIV1_MASK               64U
#define ADCCFG_ADLPC_MASK               128U
#define ADCCFG_ADICLK_MASK              3U
#define ADCCFG_ADICLK_BITNUM            0U
#define ADCCFG_MODE_MASK                12U
#define ADCCFG_MODE_BITNUM              2U
#define ADCCFG_ADIV_MASK                96U
#define ADCCFG_ADIV_BITNUM              5U


/*** APCTL1 - Pin Control 1 Register; 0x00000017 ***/
typedef union {
  byte Byte;
  struct {
    byte ADPC0       :1;                                       /* ADC Pin Control 0 - ADPC0 is used to control the pin associated with channel AD0 */
    byte ADPC1       :1;                                       /* ADC Pin Control 1 - ADPC1 is used to control the pin associated with channel AD1 */
    byte ADPC2       :1;                                       /* ADC Pin Control 2 - ADPC2 is used to control the pin associated with channel AD2 */
    byte ADPC3       :1;                                       /* ADC Pin Control 3 - ADPC3 is used to control the pin associated with channel AD3 */
    byte ADPC4       :1;                                       /* ADC Pin Control 4 - ADPC4 is used to control the pin associated with channel AD4 */
    byte ADPC5       :1;                                       /* ADC Pin Control 5 - ADPC5 is used to control the pin associated with channel AD5 */
    byte ADPC6       :1;                                       /* ADC Pin Control 6 - ADPC6 is used to control the pin associated with channel AD6 */
    byte ADPC7       :1;                                       /* ADC Pin Control 7 - ADPC7 is used to control the pin associated with channel AD7 */
  } Bits;
} APCTL1STR;
extern volatile APCTL1STR _APCTL1 @0x00000017;
#define APCTL1                          _APCTL1.Byte
#define APCTL1_ADPC0                    _APCTL1.Bits.ADPC0
#define APCTL1_ADPC1                    _APCTL1.Bits.ADPC1
#define APCTL1_ADPC2                    _APCTL1.Bits.ADPC2
#define APCTL1_ADPC3                    _APCTL1.Bits.ADPC3
#define APCTL1_ADPC4                    _APCTL1.Bits.ADPC4
#define APCTL1_ADPC5                    _APCTL1.Bits.ADPC5
#define APCTL1_ADPC6                    _APCTL1.Bits.ADPC6
#define APCTL1_ADPC7                    _APCTL1.Bits.ADPC7

#define APCTL1_ADPC0_MASK               1U
#define APCTL1_ADPC1_MASK               2U
#define APCTL1_ADPC2_MASK               4U
#define APCTL1_ADPC3_MASK               8U
#define APCTL1_ADPC4_MASK               16U
#define APCTL1_ADPC5_MASK               32U
#define APCTL1_ADPC6_MASK               64U
#define APCTL1_ADPC7_MASK               128U


/*** APCTL2 - Pin Control 2 Register; 0x00000018 ***/
typedef union {
  byte Byte;
  struct {
    byte ADPC8       :1;                                       /* ADC Pin Control 8 - ADPC8 is used to control the pin associated with channel AD8 */
    byte ADPC9       :1;                                       /* ADC Pin Control 9 - ADPC9 is used to control the pin associated with channel AD9 */
    byte ADPC10      :1;                                       /* ADC Pin Control 10 - ADPC10 is used to control the pin associated with channel AD10 */
    byte ADPC11      :1;                                       /* ADC Pin Control 11 - ADPC11 is used to control the pin associated with channel AD11 */
    byte ADPC12      :1;                                       /* ADC Pin Control 12 - ADPC12 is used to control the pin associated with channel AD12 */
    byte ADPC13      :1;                                       /* ADC Pin Control 13 - ADPC13 is used to control the pin associated with channel AD13 */
    byte ADPC14      :1;                                       /* ADC Pin Control 14 - ADPC14 is used to control the pin associated with channel AD14 */
    byte ADPC15      :1;                                       /* ADC Pin Control 15 - ADPC15 is used to control the pin associated with channel AD15 */
  } Bits;
} APCTL2STR;
extern volatile APCTL2STR _APCTL2 @0x00000018;
#define APCTL2                          _APCTL2.Byte
#define APCTL2_ADPC8                    _APCTL2.Bits.ADPC8
#define APCTL2_ADPC9                    _APCTL2.Bits.ADPC9
#define APCTL2_ADPC10                   _APCTL2.Bits.ADPC10
#define APCTL2_ADPC11                   _APCTL2.Bits.ADPC11
#define APCTL2_ADPC12                   _APCTL2.Bits.ADPC12
#define APCTL2_ADPC13                   _APCTL2.Bits.ADPC13
#define APCTL2_ADPC14                   _APCTL2.Bits.ADPC14
#define APCTL2_ADPC15                   _APCTL2.Bits.ADPC15

#define APCTL2_ADPC8_MASK               1U
#define APCTL2_ADPC9_MASK               2U
#define APCTL2_ADPC10_MASK              4U
#define APCTL2_ADPC11_MASK              8U
#define APCTL2_ADPC12_MASK              16U
#define APCTL2_ADPC13_MASK              32U
#define APCTL2_ADPC14_MASK              64U
#define APCTL2_ADPC15_MASK              128U


/*** APCTL3 - Pin Control 3 Register; 0x00000019 ***/
typedef union {
  byte Byte;
  struct {
    byte ADPC16      :1;                                       /* ADC Pin Control 16 - ADPC16 is used to control the pin associated with channel AD16 */
    byte ADPC17      :1;                                       /* ADC Pin Control 17 - ADPC17 is used to control the pin associated with channel AD17 */
    byte ADPC18      :1;                                       /* ADC Pin Control 18 - ADPC18 is used to control the pin associated with channel AD18 */
    byte ADPC19      :1;                                       /* ADC Pin Control 19 - ADPC19 is used to control the pin associated with channel AD19 */
    byte ADPC20      :1;                                       /* ADC Pin Control 20 - ADPC20 is used to control the pin associated with channel AD20 */
    byte ADPC21      :1;                                       /* ADC Pin Control 21 - ADPC21 is used to control the pin associated with channel AD21 */
    byte ADPC22      :1;                                       /* ADC Pin Control 22 - ADPC22 is used to control the pin associated with channel AD22 */
    byte ADPC23      :1;                                       /* ADC Pin Control 23 - ADPC23 is used to control the pin associated with channel AD23 */
  } Bits;
} APCTL3STR;
extern volatile APCTL3STR _APCTL3 @0x00000019;
#define APCTL3                          _APCTL3.Byte
#define APCTL3_ADPC16                   _APCTL3.Bits.ADPC16
#define APCTL3_ADPC17                   _APCTL3.Bits.ADPC17
#define APCTL3_ADPC18                   _APCTL3.Bits.ADPC18
#define APCTL3_ADPC19                   _APCTL3.Bits.ADPC19
#define APCTL3_ADPC20                   _APCTL3.Bits.ADPC20
#define APCTL3_ADPC21                   _APCTL3.Bits.ADPC21
#define APCTL3_ADPC22                   _APCTL3.Bits.ADPC22
#define APCTL3_ADPC23                   _APCTL3.Bits.ADPC23

#define APCTL3_ADPC16_MASK              1U
#define APCTL3_ADPC17_MASK              2U
#define APCTL3_ADPC18_MASK              4U
#define APCTL3_ADPC19_MASK              8U
#define APCTL3_ADPC20_MASK              16U
#define APCTL3_ADPC21_MASK              32U
#define APCTL3_ADPC22_MASK              64U
#define APCTL3_ADPC23_MASK              128U


/*** ACMP1SC - ACMP1 Status and Control Register; 0x0000001A ***/
typedef union {
  byte Byte;
  struct {
    byte ACMOD0      :1;                                       /* Analog Comparator Mode Bit 0 */
    byte ACMOD1      :1;                                       /* Analog Comparator Mode Bit 1 */
    byte ACOPE       :1;                                       /* Analog Comparator Output Pin Enable */
    byte ACO         :1;                                       /* Analog Comparator Output */
    byte ACIE        :1;                                       /* Analog Comparator Interrupt Enable */
    byte ACF         :1;                                       /* Analog Comparator Flag */
    byte ACBGS       :1;                                       /* Analog Comparator Bandgap Select */
    byte ACME        :1;                                       /* Analog Comparator Module Enable */
  } Bits;
  struct {
    byte grpACMOD :2;
    byte         :1;
    byte         :1;
    byte         :1;
    byte         :1;
    byte         :1;
    byte         :1;
  } MergedBits;
} ACMP1SCSTR;
extern volatile ACMP1SCSTR _ACMP1SC @0x0000001A;
#define ACMP1SC                         _ACMP1SC.Byte
#define ACMP1SC_ACMOD0                  _ACMP1SC.Bits.ACMOD0
#define ACMP1SC_ACMOD1                  _ACMP1SC.Bits.ACMOD1
#define ACMP1SC_ACOPE                   _ACMP1SC.Bits.ACOPE
#define ACMP1SC_ACO                     _ACMP1SC.Bits.ACO
#define ACMP1SC_ACIE                    _ACMP1SC.Bits.ACIE
#define ACMP1SC_ACF                     _ACMP1SC.Bits.ACF
#define ACMP1SC_ACBGS                   _ACMP1SC.Bits.ACBGS
#define ACMP1SC_ACME                    _ACMP1SC.Bits.ACME
#define ACMP1SC_ACMOD                   _ACMP1SC.MergedBits.grpACMOD

#define ACMP1SC_ACMOD0_MASK             1U
#define ACMP1SC_ACMOD1_MASK             2U
#define ACMP1SC_ACOPE_MASK              4U
#define ACMP1SC_ACO_MASK                8U
#define ACMP1SC_ACIE_MASK               16U
#define ACMP1SC_ACF_MASK                32U
#define ACMP1SC_ACBGS_MASK              64U
#define ACMP1SC_ACME_MASK               128U
#define ACMP1SC_ACMOD_MASK              3U
#define ACMP1SC_ACMOD_BITNUM            0U


/*** ACMP2SC - ACMP2 Status and Control Register; 0x0000001B ***/
typedef union {
  byte Byte;
  struct {
    byte ACMOD0      :1;                                       /* Analog Comparator Mode Bit 0 */
    byte ACMOD1      :1;                                       /* Analog Comparator Mode Bit 1 */
    byte ACOPE       :1;                                       /* Analog Comparator Output Pin Enable */
    byte ACO         :1;                                       /* Analog Comparator Output */
    byte ACIE        :1;                                       /* Analog Comparator Interrupt Enable */
    byte ACF         :1;                                       /* Analog Comparator Flag */
    byte ACBGS       :1;                                       /* Analog Comparator Bandgap Select */
    byte ACME        :1;                                       /* Analog Comparator Module Enable */
  } Bits;
  struct {
    byte grpACMOD :2;
    byte         :1;
    byte         :1;
    byte         :1;
    byte         :1;
    byte         :1;
    byte         :1;
  } MergedBits;
} ACMP2SCSTR;
extern volatile ACMP2SCSTR _ACMP2SC @0x0000001B;
#define ACMP2SC                         _ACMP2SC.Byte
#define ACMP2SC_ACMOD0                  _ACMP2SC.Bits.ACMOD0
#define ACMP2SC_ACMOD1                  _ACMP2SC.Bits.ACMOD1
#define ACMP2SC_ACOPE                   _ACMP2SC.Bits.ACOPE
#define ACMP2SC_ACO                     _ACMP2SC.Bits.ACO
#define ACMP2SC_ACIE                    _ACMP2SC.Bits.ACIE
#define ACMP2SC_ACF                     _ACMP2SC.Bits.ACF
#define ACMP2SC_ACBGS                   _ACMP2SC.Bits.ACBGS
#define ACMP2SC_ACME                    _ACMP2SC.Bits.ACME
#define ACMP2SC_ACMOD                   _ACMP2SC.MergedBits.grpACMOD

#define ACMP2SC_ACMOD0_MASK             1U
#define ACMP2SC_ACMOD1_MASK             2U
#define ACMP2SC_ACOPE_MASK              4U
#define ACMP2SC_ACO_MASK                8U
#define ACMP2SC_ACIE_MASK               16U
#define ACMP2SC_ACF_MASK                32U
#define ACMP2SC_ACBGS_MASK              64U
#define ACMP2SC_ACME_MASK               128U
#define ACMP2SC_ACMOD_MASK              3U
#define ACMP2SC_ACMOD_BITNUM            0U


/*** PTGD - Port G Data Register; 0x0000001C ***/
typedef union {
  byte Byte;
  struct {
    byte PTGD0       :1;                                       /* Port G Data Register Bit 0 */
    byte PTGD1       :1;                                       /* Port G Data Register Bit 1 */
    byte PTGD2       :1;                                       /* Port G Data Register Bit 2 */
    byte PTGD3       :1;                                       /* Port G Data Register Bit 3 */
    byte PTGD4       :1;                                       /* Port G Data Register Bit 4 */
    byte PTGD5       :1;                                       /* Port G Data Register Bit 5 */
    byte PTGD6       :1;                                       /* Port G Data Register Bit 6 */
    byte PTGD7       :1;                                       /* Port G Data Register Bit 7 */
  } Bits;
} PTGDSTR;
extern volatile PTGDSTR _PTGD @0x0000001C;
#define PTGD                            _PTGD.Byte
#define PTGD_PTGD0                      _PTGD.Bits.PTGD0
#define PTGD_PTGD1                      _PTGD.Bits.PTGD1
#define PTGD_PTGD2                      _PTGD.Bits.PTGD2
#define PTGD_PTGD3                      _PTGD.Bits.PTGD3
#define PTGD_PTGD4                      _PTGD.Bits.PTGD4
#define PTGD_PTGD5                      _PTGD.Bits.PTGD5
#define PTGD_PTGD6                      _PTGD.Bits.PTGD6
#define PTGD_PTGD7                      _PTGD.Bits.PTGD7

#define PTGD_PTGD0_MASK                 1U
#define PTGD_PTGD1_MASK                 2U
#define PTGD_PTGD2_MASK                 4U
#define PTGD_PTGD3_MASK                 8U
#define PTGD_PTGD4_MASK                 16U
#define PTGD_PTGD5_MASK                 32U
#define PTGD_PTGD6_MASK                 64U
#define PTGD_PTGD7_MASK                 128U


/*** PTGDD - Port G Data Direction Register; 0x0000001D ***/
typedef union {
  byte Byte;
  struct {
    byte PTGDD0      :1;                                       /* Data Direction for Port G Bit 0 */
    byte PTGDD1      :1;                                       /* Data Direction for Port G Bit 1 */
    byte PTGDD2      :1;                                       /* Data Direction for Port G Bit 2 */
    byte PTGDD3      :1;                                       /* Data Direction for Port G Bit 3 */
    byte PTGDD4      :1;                                       /* Data Direction for Port G Bit 4 */
    byte PTGDD5      :1;                                       /* Data Direction for Port G Bit 5 */
    byte PTGDD6      :1;                                       /* Data Direction for Port G Bit 6 */
    byte PTGDD7      :1;                                       /* Data Direction for Port G Bit 7 */
  } Bits;
} PTGDDSTR;
extern volatile PTGDDSTR _PTGDD @0x0000001D;
#define PTGDD                           _PTGDD.Byte
#define PTGDD_PTGDD0                    _PTGDD.Bits.PTGDD0
#define PTGDD_PTGDD1                    _PTGDD.Bits.PTGDD1
#define PTGDD_PTGDD2                    _PTGDD.Bits.PTGDD2
#define PTGDD_PTGDD3                    _PTGDD.Bits.PTGDD3
#define PTGDD_PTGDD4                    _PTGDD.Bits.PTGDD4
#define PTGDD_PTGDD5                    _PTGDD.Bits.PTGDD5
#define PTGDD_PTGDD6                    _PTGDD.Bits.PTGDD6
#define PTGDD_PTGDD7                    _PTGDD.Bits.PTGDD7

#define PTGDD_PTGDD0_MASK               1U
#define PTGDD_PTGDD1_MASK               2U
#define PTGDD_PTGDD2_MASK               4U
#define PTGDD_PTGDD3_MASK               8U
#define PTGDD_PTGDD4_MASK               16U
#define PTGDD_PTGDD5_MASK               32U
#define PTGDD_PTGDD6_MASK               64U
#define PTGDD_PTGDD7_MASK               128U


/*** PTHD - Port H Data Register; 0x0000001E ***/
typedef union {
  byte Byte;
  struct {
    byte PTHD0       :1;                                       /* Port H Data Register Bit 0 */
    byte PTHD1       :1;                                       /* Port H Data Register Bit 1 */
    byte PTHD2       :1;                                       /* Port H Data Register Bit 2 */
    byte PTHD3       :1;                                       /* Port H Data Register Bit 3 */
    byte PTHD4       :1;                                       /* Port H Data Register Bit 4 */
    byte PTHD5       :1;                                       /* Port H Data Register Bit 5 */
    byte PTHD6       :1;                                       /* Port H Data Register Bit 6 */
    byte PTHD7       :1;                                       /* Port H Data Register Bit 7 */
  } Bits;
} PTHDSTR;
extern volatile PTHDSTR _PTHD @0x0000001E;
#define PTHD                            _PTHD.Byte
#define PTHD_PTHD0                      _PTHD.Bits.PTHD0
#define PTHD_PTHD1                      _PTHD.Bits.PTHD1
#define PTHD_PTHD2                      _PTHD.Bits.PTHD2
#define PTHD_PTHD3                      _PTHD.Bits.PTHD3
#define PTHD_PTHD4                      _PTHD.Bits.PTHD4
#define PTHD_PTHD5                      _PTHD.Bits.PTHD5
#define PTHD_PTHD6                      _PTHD.Bits.PTHD6
#define PTHD_PTHD7                      _PTHD.Bits.PTHD7

#define PTHD_PTHD0_MASK                 1U
#define PTHD_PTHD1_MASK                 2U
#define PTHD_PTHD2_MASK                 4U
#define PTHD_PTHD3_MASK                 8U
#define PTHD_PTHD4_MASK                 16U
#define PTHD_PTHD5_MASK                 32U
#define PTHD_PTHD6_MASK                 64U
#define PTHD_PTHD7_MASK                 128U


/*** PTHDD - Port H Data Direction Register; 0x0000001F ***/
typedef union {
  byte Byte;
  struct {
    byte PTHDD0      :1;                                       /* Data Direction for Port H Bit 0 */
    byte PTHDD1      :1;                                       /* Data Direction for Port H Bit 1 */
    byte PTHDD2      :1;                                       /* Data Direction for Port H Bit 2 */
    byte PTHDD3      :1;                                       /* Data Direction for Port H Bit 3 */
    byte PTHDD4      :1;                                       /* Data Direction for Port H Bit 4 */
    byte PTHDD5      :1;                                       /* Data Direction for Port H Bit 5 */
    byte PTHDD6      :1;                                       /* Data Direction for Port H Bit 6 */
    byte PTHDD7      :1;                                       /* Data Direction for Port H Bit 7 */
  } Bits;
} PTHDDSTR;
extern volatile PTHDDSTR _PTHDD @0x0000001F;
#define PTHDD                           _PTHDD.Byte
#define PTHDD_PTHDD0                    _PTHDD.Bits.PTHDD0
#define PTHDD_PTHDD1                    _PTHDD.Bits.PTHDD1
#define PTHDD_PTHDD2                    _PTHDD.Bits.PTHDD2
#define PTHDD_PTHDD3                    _PTHDD.Bits.PTHDD3
#define PTHDD_PTHDD4                    _PTHDD.Bits.PTHDD4
#define PTHDD_PTHDD5                    _PTHDD.Bits.PTHDD5
#define PTHDD_PTHDD6                    _PTHDD.Bits.PTHDD6
#define PTHDD_PTHDD7                    _PTHDD.Bits.PTHDD7

#define PTHDD_PTHDD0_MASK               1U
#define PTHDD_PTHDD1_MASK               2U
#define PTHDD_PTHDD2_MASK               4U
#define PTHDD_PTHDD3_MASK               8U
#define PTHDD_PTHDD4_MASK               16U
#define PTHDD_PTHDD5_MASK               32U
#define PTHDD_PTHDD6_MASK               64U
#define PTHDD_PTHDD7_MASK               128U


/*** SCI1BD - SCI1 Baud Rate Register; 0x00000020 ***/
typedef union {
  word Word;
   /* Overlapped registers: */
  struct {
    /*** SCI1BDH - SCI1 Baud Rate Register High; 0x00000020 ***/
    union {
      byte Byte;
      struct {
        byte SBR8        :1;                                       /* Baud Rate Modulo Divisor Bit 8 */
        byte SBR9        :1;                                       /* Baud Rate Modulo Divisor Bit 9 */
        byte SBR10       :1;                                       /* Baud Rate Modulo Divisor Bit 10 */
        byte SBR11       :1;                                       /* Baud Rate Modulo Divisor Bit 11 */
        byte SBR12       :1;                                       /* Baud Rate Modulo Divisor Bit 12 */
        byte             :1; 
        byte RXEDGIE     :1;                                       /* RxD Input Active Edge Interrupt Enable (for RXEDGIF) */
        byte LBKDIE      :1;                                       /* LIN Break Detect Interrupt Enable (for LBKDIF) */
      } Bits;
      struct {
        byte grpSBR_8 :5;
        byte     :1;
        byte     :1;
        byte     :1;
      } MergedBits;
    } SCI1BDHSTR;
    #define SCI1BDH                     _SCI1BD.Overlap_STR.SCI1BDHSTR.Byte
    #define SCI1BDH_SBR8                _SCI1BD.Overlap_STR.SCI1BDHSTR.Bits.SBR8
    #define SCI1BDH_SBR9                _SCI1BD.Overlap_STR.SCI1BDHSTR.Bits.SBR9
    #define SCI1BDH_SBR10               _SCI1BD.Overlap_STR.SCI1BDHSTR.Bits.SBR10
    #define SCI1BDH_SBR11               _SCI1BD.Overlap_STR.SCI1BDHSTR.Bits.SBR11
    #define SCI1BDH_SBR12               _SCI1BD.Overlap_STR.SCI1BDHSTR.Bits.SBR12
    #define SCI1BDH_RXEDGIE             _SCI1BD.Overlap_STR.SCI1BDHSTR.Bits.RXEDGIE
    #define SCI1BDH_LBKDIE              _SCI1BD.Overlap_STR.SCI1BDHSTR.Bits.LBKDIE
    #define SCI1BDH_SBR_8               _SCI1BD.Overlap_STR.SCI1BDHSTR.MergedBits.grpSBR_8
    #define SCI1BDH_SBR                 SCI1BDH_SBR_8
    
    #define SCI1BDH_SBR8_MASK           1U
    #define SCI1BDH_SBR9_MASK           2U
    #define SCI1BDH_SBR10_MASK          4U
    #define SCI1BDH_SBR11_MASK          8U
    #define SCI1BDH_SBR12_MASK          16U
    #define SCI1BDH_RXEDGIE_MASK        64U
    #define SCI1BDH_LBKDIE_MASK         128U
    #define SCI1BDH_SBR_8_MASK          31U
    #define SCI1BDH_SBR_8_BITNUM        0U
    

    /*** SCI1BDL - SCI1 Baud Rate Register Low; 0x00000021 ***/
    union {
      byte Byte;
      struct {
        byte SBR0        :1;                                       /* Baud Rate Modulo Divisor Bit 0 */
        byte SBR1        :1;                                       /* Baud Rate Modulo Divisor Bit 1 */
        byte SBR2        :1;                                       /* Baud Rate Modulo Divisor Bit 2 */
        byte SBR3        :1;                                       /* Baud Rate Modulo Divisor Bit 3 */
        byte SBR4        :1;                                       /* Baud Rate Modulo Divisor Bit 4 */
        byte SBR5        :1;                                       /* Baud Rate Modulo Divisor Bit 5 */
        byte SBR6        :1;                                       /* Baud Rate Modulo Divisor Bit 6 */
        byte SBR7        :1;                                       /* Baud Rate Modulo Divisor Bit 7 */
      } Bits;
    } SCI1BDLSTR;
    #define SCI1BDL                     _SCI1BD.Overlap_STR.SCI1BDLSTR.Byte
    #define SCI1BDL_SBR0                _SCI1BD.Overlap_STR.SCI1BDLSTR.Bits.SBR0
    #define SCI1BDL_SBR1                _SCI1BD.Overlap_STR.SCI1BDLSTR.Bits.SBR1
    #define SCI1BDL_SBR2                _SCI1BD.Overlap_STR.SCI1BDLSTR.Bits.SBR2
    #define SCI1BDL_SBR3                _SCI1BD.Overlap_STR.SCI1BDLSTR.Bits.SBR3
    #define SCI1BDL_SBR4                _SCI1BD.Overlap_STR.SCI1BDLSTR.Bits.SBR4
    #define SCI1BDL_SBR5                _SCI1BD.Overlap_STR.SCI1BDLSTR.Bits.SBR5
    #define SCI1BDL_SBR6                _SCI1BD.Overlap_STR.SCI1BDLSTR.Bits.SBR6
    #define SCI1BDL_SBR7                _SCI1BD.Overlap_STR.SCI1BDLSTR.Bits.SBR7
    
    #define SCI1BDL_SBR0_MASK           1U
    #define SCI1BDL_SBR1_MASK           2U
    #define SCI1BDL_SBR2_MASK           4U
    #define SCI1BDL_SBR3_MASK           8U
    #define SCI1BDL_SBR4_MASK           16U
    #define SCI1BDL_SBR5_MASK           32U
    #define SCI1BDL_SBR6_MASK           64U
    #define SCI1BDL_SBR7_MASK           128U
    
  } Overlap_STR;

} SCI1BDSTR;
extern volatile SCI1BDSTR _SCI1BD @0x00000020;
#define SCI1BD                          _SCI1BD.Word


/*** SCI1C1 - SCI1 Control Register 1; 0x00000022 ***/
typedef union {
  byte Byte;
  struct {
    byte PT          :1;                                       /* Parity Type */
    byte PE          :1;                                       /* Parity Enable */
    byte ILT         :1;                                       /* Idle Line Type Select */
    byte WAKE        :1;                                       /* Receiver Wakeup Method Select */
    byte M           :1;                                       /* 9-Bit or 8-Bit Mode Select */
    byte RSRC        :1;                                       /* Receiver Source Select */
    byte SCISWAI     :1;                                       /* SCI Stops in Wait Mode */
    byte LOOPS       :1;                                       /* Loop Mode Select */
  } Bits;
} SCI1C1STR;
extern volatile SCI1C1STR _SCI1C1 @0x00000022;
#define SCI1C1                          _SCI1C1.Byte
#define SCI1C1_PT                       _SCI1C1.Bits.PT
#define SCI1C1_PE                       _SCI1C1.Bits.PE
#define SCI1C1_ILT                      _SCI1C1.Bits.ILT
#define SCI1C1_WAKE                     _SCI1C1.Bits.WAKE
#define SCI1C1_M                        _SCI1C1.Bits.M
#define SCI1C1_RSRC                     _SCI1C1.Bits.RSRC
#define SCI1C1_SCISWAI                  _SCI1C1.Bits.SCISWAI
#define SCI1C1_LOOPS                    _SCI1C1.Bits.LOOPS

#define SCI1C1_PT_MASK                  1U
#define SCI1C1_PE_MASK                  2U
#define SCI1C1_ILT_MASK                 4U
#define SCI1C1_WAKE_MASK                8U
#define SCI1C1_M_MASK                   16U
#define SCI1C1_RSRC_MASK                32U
#define SCI1C1_SCISWAI_MASK             64U
#define SCI1C1_LOOPS_MASK               128U


/*** SCI1C2 - SCI1 Control Register 2; 0x00000023 ***/
typedef union {
  byte Byte;
  struct {
    byte SBK         :1;                                       /* Send Break */
    byte RWU         :1;                                       /* Receiver Wakeup Control */
    byte RE          :1;                                       /* Receiver Enable */
    byte TE          :1;                                       /* Transmitter Enable */
    byte ILIE        :1;                                       /* Idle Line Interrupt Enable (for IDLE) */
    byte RIE         :1;                                       /* Receiver Interrupt Enable (for RDRF) */
    byte TCIE        :1;                                       /* Transmission Complete Interrupt Enable (for TC) */
    byte TIE         :1;                                       /* Transmit Interrupt Enable (for TDRE) */
  } Bits;
} SCI1C2STR;
extern volatile SCI1C2STR _SCI1C2 @0x00000023;
#define SCI1C2                          _SCI1C2.Byte
#define SCI1C2_SBK                      _SCI1C2.Bits.SBK
#define SCI1C2_RWU                      _SCI1C2.Bits.RWU
#define SCI1C2_RE                       _SCI1C2.Bits.RE
#define SCI1C2_TE                       _SCI1C2.Bits.TE
#define SCI1C2_ILIE                     _SCI1C2.Bits.ILIE
#define SCI1C2_RIE                      _SCI1C2.Bits.RIE
#define SCI1C2_TCIE                     _SCI1C2.Bits.TCIE
#define SCI1C2_TIE                      _SCI1C2.Bits.TIE

#define SCI1C2_SBK_MASK                 1U
#define SCI1C2_RWU_MASK                 2U
#define SCI1C2_RE_MASK                  4U
#define SCI1C2_TE_MASK                  8U
#define SCI1C2_ILIE_MASK                16U
#define SCI1C2_RIE_MASK                 32U
#define SCI1C2_TCIE_MASK                64U
#define SCI1C2_TIE_MASK                 128U


/*** SCI1S1 - SCI1 Status Register 1; 0x00000024 ***/
typedef union {
  byte Byte;
  struct {
    byte PF          :1;                                       /* Parity Error Flag */
    byte FE          :1;                                       /* Framing Error Flag */
    byte NF          :1;                                       /* Noise Flag */
    byte OR          :1;                                       /* Receiver Overrun Flag */
    byte IDLE        :1;                                       /* Idle Line Flag */
    byte RDRF        :1;                                       /* Receive Data Register Full Flag */
    byte TC          :1;                                       /* Transmission Complete Flag */
    byte TDRE        :1;                                       /* Transmit Data Register Empty Flag */
  } Bits;
} SCI1S1STR;
extern volatile SCI1S1STR _SCI1S1 @0x00000024;
#define SCI1S1                          _SCI1S1.Byte
#define SCI1S1_PF                       _SCI1S1.Bits.PF
#define SCI1S1_FE                       _SCI1S1.Bits.FE
#define SCI1S1_NF                       _SCI1S1.Bits.NF
#define SCI1S1_OR                       _SCI1S1.Bits.OR
#define SCI1S1_IDLE                     _SCI1S1.Bits.IDLE
#define SCI1S1_RDRF                     _SCI1S1.Bits.RDRF
#define SCI1S1_TC                       _SCI1S1.Bits.TC
#define SCI1S1_TDRE                     _SCI1S1.Bits.TDRE

#define SCI1S1_PF_MASK                  1U
#define SCI1S1_FE_MASK                  2U
#define SCI1S1_NF_MASK                  4U
#define SCI1S1_OR_MASK                  8U
#define SCI1S1_IDLE_MASK                16U
#define SCI1S1_RDRF_MASK                32U
#define SCI1S1_TC_MASK                  64U
#define SCI1S1_TDRE_MASK                128U


/*** SCI1S2 - SCI1 Status Register 2; 0x00000025 ***/
typedef union {
  byte Byte;
  struct {
    byte RAF         :1;                                       /* Receiver Active Flag */
    byte LBKDE       :1;                                       /* LIN Break Detection Enable */
    byte BRK13       :1;                                       /* Break Character Generation Length */
    byte RWUID       :1;                                       /* Receive Wake Up Idle Detect */
    byte RXINV       :1;                                       /* Receive Data Inversion */
    byte             :1; 
    byte RXEDGIF     :1;                                       /* RxD Pin Active Edge Interrupt Flag */
    byte LBKDIF      :1;                                       /* LIN Break Detect Interrupt Flag */
  } Bits;
} SCI1S2STR;
extern volatile SCI1S2STR _SCI1S2 @0x00000025;
#define SCI1S2                          _SCI1S2.Byte
#define SCI1S2_RAF                      _SCI1S2.Bits.RAF
#define SCI1S2_LBKDE                    _SCI1S2.Bits.LBKDE
#define SCI1S2_BRK13                    _SCI1S2.Bits.BRK13
#define SCI1S2_RWUID                    _SCI1S2.Bits.RWUID
#define SCI1S2_RXINV                    _SCI1S2.Bits.RXINV
#define SCI1S2_RXEDGIF                  _SCI1S2.Bits.RXEDGIF
#define SCI1S2_LBKDIF                   _SCI1S2.Bits.LBKDIF

#define SCI1S2_RAF_MASK                 1U
#define SCI1S2_LBKDE_MASK               2U
#define SCI1S2_BRK13_MASK               4U
#define SCI1S2_RWUID_MASK               8U
#define SCI1S2_RXINV_MASK               16U
#define SCI1S2_RXEDGIF_MASK             64U
#define SCI1S2_LBKDIF_MASK              128U


/*** SCI1C3 - SCI1 Control Register 3; 0x00000026 ***/
typedef union {
  byte Byte;
  struct {
    byte PEIE        :1;                                       /* Parity Error Interrupt Enable */
    byte FEIE        :1;                                       /* Framing Error Interrupt Enable */
    byte NEIE        :1;                                       /* Noise Error Interrupt Enable */
    byte ORIE        :1;                                       /* Overrun Interrupt Enable */
    byte TXINV       :1;                                       /* Transmit Data Inversion */
    byte TXDIR       :1;                                       /* TxD Pin Direction in Single-Wire Mode */
    byte T8          :1;                                       /* Ninth Data Bit for Transmitter */
    byte R8          :1;                                       /* Ninth Data Bit for Receiver */
  } Bits;
} SCI1C3STR;
extern volatile SCI1C3STR _SCI1C3 @0x00000026;
#define SCI1C3                          _SCI1C3.Byte
#define SCI1C3_PEIE                     _SCI1C3.Bits.PEIE
#define SCI1C3_FEIE                     _SCI1C3.Bits.FEIE
#define SCI1C3_NEIE                     _SCI1C3.Bits.NEIE
#define SCI1C3_ORIE                     _SCI1C3.Bits.ORIE
#define SCI1C3_TXINV                    _SCI1C3.Bits.TXINV
#define SCI1C3_TXDIR                    _SCI1C3.Bits.TXDIR
#define SCI1C3_T8                       _SCI1C3.Bits.T8
#define SCI1C3_R8                       _SCI1C3.Bits.R8

#define SCI1C3_PEIE_MASK                1U
#define SCI1C3_FEIE_MASK                2U
#define SCI1C3_NEIE_MASK                4U
#define SCI1C3_ORIE_MASK                8U
#define SCI1C3_TXINV_MASK               16U
#define SCI1C3_TXDIR_MASK               32U
#define SCI1C3_T8_MASK                  64U
#define SCI1C3_R8_MASK                  128U


/*** SCI1D - SCI1 Data Register; 0x00000027 ***/
typedef union {
  byte Byte;
  struct {
    byte R0_T0       :1;                                       /* Receive/Transmit Data Bit 0 */
    byte R1_T1       :1;                                       /* Receive/Transmit Data Bit 1 */
    byte R2_T2       :1;                                       /* Receive/Transmit Data Bit 2 */
    byte R3_T3       :1;                                       /* Receive/Transmit Data Bit 3 */
    byte R4_T4       :1;                                       /* Receive/Transmit Data Bit 4 */
    byte R5_T5       :1;                                       /* Receive/Transmit Data Bit 5 */
    byte R6_T6       :1;                                       /* Receive/Transmit Data Bit 6 */
    byte R7_T7       :1;                                       /* Receive/Transmit Data Bit 7 */
  } Bits;
} SCI1DSTR;
extern volatile SCI1DSTR _SCI1D @0x00000027;
#define SCI1D                           _SCI1D.Byte
#define SCI1D_R0_T0                     _SCI1D.Bits.R0_T0
#define SCI1D_R1_T1                     _SCI1D.Bits.R1_T1
#define SCI1D_R2_T2                     _SCI1D.Bits.R2_T2
#define SCI1D_R3_T3                     _SCI1D.Bits.R3_T3
#define SCI1D_R4_T4                     _SCI1D.Bits.R4_T4
#define SCI1D_R5_T5                     _SCI1D.Bits.R5_T5
#define SCI1D_R6_T6                     _SCI1D.Bits.R6_T6
#define SCI1D_R7_T7                     _SCI1D.Bits.R7_T7

#define SCI1D_R0_T0_MASK                1U
#define SCI1D_R1_T1_MASK                2U
#define SCI1D_R2_T2_MASK                4U
#define SCI1D_R3_T3_MASK                8U
#define SCI1D_R4_T4_MASK                16U
#define SCI1D_R5_T5_MASK                32U
#define SCI1D_R6_T6_MASK                64U
#define SCI1D_R7_T7_MASK                128U


/*** SPI1C1 - SPI1 Control Register 1; 0x00000028 ***/
typedef union {
  byte Byte;
  struct {
    byte LSBFE       :1;                                       /* LSB First (Shifter Direction) */
    byte SSOE        :1;                                       /* Slave Select Output Enable */
    byte CPHA        :1;                                       /* Clock Phase */
    byte CPOL        :1;                                       /* Clock Polarity */
    byte MSTR        :1;                                       /* Master/Slave Mode Select */
    byte SPTIE       :1;                                       /* SPI Transmit Interrupt Enable */
    byte SPE         :1;                                       /* SPI System Enable */
    byte SPIE        :1;                                       /* SPI Interrupt Enable (for SPRF and MODF) */
  } Bits;
} SPI1C1STR;
extern volatile SPI1C1STR _SPI1C1 @0x00000028;
#define SPI1C1                          _SPI1C1.Byte
#define SPI1C1_LSBFE                    _SPI1C1.Bits.LSBFE
#define SPI1C1_SSOE                     _SPI1C1.Bits.SSOE
#define SPI1C1_CPHA                     _SPI1C1.Bits.CPHA
#define SPI1C1_CPOL                     _SPI1C1.Bits.CPOL
#define SPI1C1_MSTR                     _SPI1C1.Bits.MSTR
#define SPI1C1_SPTIE                    _SPI1C1.Bits.SPTIE
#define SPI1C1_SPE                      _SPI1C1.Bits.SPE
#define SPI1C1_SPIE                     _SPI1C1.Bits.SPIE

#define SPI1C1_LSBFE_MASK               1U
#define SPI1C1_SSOE_MASK                2U
#define SPI1C1_CPHA_MASK                4U
#define SPI1C1_CPOL_MASK                8U
#define SPI1C1_MSTR_MASK                16U
#define SPI1C1_SPTIE_MASK               32U
#define SPI1C1_SPE_MASK                 64U
#define SPI1C1_SPIE_MASK                128U


/*** SPI1C2 - SPI1 Control Register 2; 0x00000029 ***/
typedef union {
  byte Byte;
  struct {
    byte SPC0        :1;                                       /* SPI Pin Control 0 */
    byte SPISWAI     :1;                                       /* SPI Stop in Wait Mode */
    byte             :1; 
    byte BIDIROE     :1;                                       /* Bidirectional Mode Output Enable */
    byte MODFEN      :1;                                       /* Master Mode-Fault Function Enable */
    byte             :1; 
    byte             :1; 
    byte             :1; 
  } Bits;
} SPI1C2STR;
extern volatile SPI1C2STR _SPI1C2 @0x00000029;
#define SPI1C2                          _SPI1C2.Byte
#define SPI1C2_SPC0                     _SPI1C2.Bits.SPC0
#define SPI1C2_SPISWAI                  _SPI1C2.Bits.SPISWAI
#define SPI1C2_BIDIROE                  _SPI1C2.Bits.BIDIROE
#define SPI1C2_MODFEN                   _SPI1C2.Bits.MODFEN

#define SPI1C2_SPC0_MASK                1U
#define SPI1C2_SPISWAI_MASK             2U
#define SPI1C2_BIDIROE_MASK             8U
#define SPI1C2_MODFEN_MASK              16U


/*** SPI1BR - SPI1 Baud Rate Register; 0x0000002A ***/
typedef union {
  byte Byte;
  struct {
    byte SPR0        :1;                                       /* SPI Baud Rate Divisor Bit 0 */
    byte SPR1        :1;                                       /* SPI Baud Rate Divisor Bit 1 */
    byte SPR2        :1;                                       /* SPI Baud Rate Divisor Bit 2 */
    byte             :1; 
    byte SPPR0       :1;                                       /* SPI Baud Rate Prescale Divisor Bit 0 */
    byte SPPR1       :1;                                       /* SPI Baud Rate Prescale Divisor Bit 1 */
    byte SPPR2       :1;                                       /* SPI Baud Rate Prescale Divisor Bit 2 */
    byte             :1; 
  } Bits;
  struct {
    byte grpSPR  :3;
    byte         :1;
    byte grpSPPR :3;
    byte         :1;
  } MergedBits;
} SPI1BRSTR;
extern volatile SPI1BRSTR _SPI1BR @0x0000002A;
#define SPI1BR                          _SPI1BR.Byte
#define SPI1BR_SPR0                     _SPI1BR.Bits.SPR0
#define SPI1BR_SPR1                     _SPI1BR.Bits.SPR1
#define SPI1BR_SPR2                     _SPI1BR.Bits.SPR2
#define SPI1BR_SPPR0                    _SPI1BR.Bits.SPPR0
#define SPI1BR_SPPR1                    _SPI1BR.Bits.SPPR1
#define SPI1BR_SPPR2                    _SPI1BR.Bits.SPPR2
#define SPI1BR_SPR                      _SPI1BR.MergedBits.grpSPR
#define SPI1BR_SPPR                     _SPI1BR.MergedBits.grpSPPR

#define SPI1BR_SPR0_MASK                1U
#define SPI1BR_SPR1_MASK                2U
#define SPI1BR_SPR2_MASK                4U
#define SPI1BR_SPPR0_MASK               16U
#define SPI1BR_SPPR1_MASK               32U
#define SPI1BR_SPPR2_MASK               64U
#define SPI1BR_SPR_MASK                 7U
#define SPI1BR_SPR_BITNUM               0U
#define SPI1BR_SPPR_MASK                112U
#define SPI1BR_SPPR_BITNUM              4U


/*** SPI1S - SPI1 Status Register; 0x0000002B ***/
typedef union {
  byte Byte;
  struct {
    byte             :1; 
    byte             :1; 
    byte             :1; 
    byte             :1; 
    byte MODF        :1;                                       /* Master Mode Fault Flag */
    byte SPTEF       :1;                                       /* SPI Transmit Buffer Empty Flag */
    byte             :1; 
    byte SPRF        :1;                                       /* SPI Read Buffer Full Flag */
  } Bits;
} SPI1SSTR;
extern volatile SPI1SSTR _SPI1S @0x0000002B;
#define SPI1S                           _SPI1S.Byte
#define SPI1S_MODF                      _SPI1S.Bits.MODF
#define SPI1S_SPTEF                     _SPI1S.Bits.SPTEF
#define SPI1S_SPRF                      _SPI1S.Bits.SPRF

#define SPI1S_MODF_MASK                 16U
#define SPI1S_SPTEF_MASK                32U
#define SPI1S_SPRF_MASK                 128U


/*** SPI1D - SPI1 Data Register; 0x0000002D ***/
typedef union {
  byte Byte;
} SPI1DSTR;
extern volatile SPI1DSTR _SPI1D @0x0000002D;
#define SPI1D                           _SPI1D.Byte


/*** PTJD - Port J Data Register; 0x0000002E ***/
typedef union {
  byte Byte;
  struct {
    byte PTJD0       :1;                                       /* Port J Data Register Bit 0 */
    byte PTJD1       :1;                                       /* Port J Data Register Bit 1 */
    byte PTJD2       :1;                                       /* Port J Data Register Bit 2 */
    byte PTJD3       :1;                                       /* Port J Data Register Bit 3 */
    byte PTJD4       :1;                                       /* Port J Data Register Bit 4 */
    byte PTJD5       :1;                                       /* Port J Data Register Bit 5 */
    byte PTJD6       :1;                                       /* Port J Data Register Bit 6 */
    byte PTJD7       :1;                                       /* Port J Data Register Bit 7 */
  } Bits;
} PTJDSTR;
extern volatile PTJDSTR _PTJD @0x0000002E;
#define PTJD                            _PTJD.Byte
#define PTJD_PTJD0                      _PTJD.Bits.PTJD0
#define PTJD_PTJD1                      _PTJD.Bits.PTJD1
#define PTJD_PTJD2                      _PTJD.Bits.PTJD2
#define PTJD_PTJD3                      _PTJD.Bits.PTJD3
#define PTJD_PTJD4                      _PTJD.Bits.PTJD4
#define PTJD_PTJD5                      _PTJD.Bits.PTJD5
#define PTJD_PTJD6                      _PTJD.Bits.PTJD6
#define PTJD_PTJD7                      _PTJD.Bits.PTJD7

#define PTJD_PTJD0_MASK                 1U
#define PTJD_PTJD1_MASK                 2U
#define PTJD_PTJD2_MASK                 4U
#define PTJD_PTJD3_MASK                 8U
#define PTJD_PTJD4_MASK                 16U
#define PTJD_PTJD5_MASK                 32U
#define PTJD_PTJD6_MASK                 64U
#define PTJD_PTJD7_MASK                 128U


/*** PTJDD - Port J Data Direction Register; 0x0000002F ***/
typedef union {
  byte Byte;
  struct {
    byte PTJDD0      :1;                                       /* Data Direction for Port J Bit 0 */
    byte PTJDD1      :1;                                       /* Data Direction for Port J Bit 1 */
    byte PTJDD2      :1;                                       /* Data Direction for Port J Bit 2 */
    byte PTJDD3      :1;                                       /* Data Direction for Port J Bit 3 */
    byte PTJDD4      :1;                                       /* Data Direction for Port J Bit 4 */
    byte PTJDD5      :1;                                       /* Data Direction for Port J Bit 5 */
    byte PTJDD6      :1;                                       /* Data Direction for Port J Bit 6 */
    byte PTJDD7      :1;                                       /* Data Direction for Port J Bit 7 */
  } Bits;
} PTJDDSTR;
extern volatile PTJDDSTR _PTJDD @0x0000002F;
#define PTJDD                           _PTJDD.Byte
#define PTJDD_PTJDD0                    _PTJDD.Bits.PTJDD0
#define PTJDD_PTJDD1                    _PTJDD.Bits.PTJDD1
#define PTJDD_PTJDD2                    _PTJDD.Bits.PTJDD2
#define PTJDD_PTJDD3                    _PTJDD.Bits.PTJDD3
#define PTJDD_PTJDD4                    _PTJDD.Bits.PTJDD4
#define PTJDD_PTJDD5                    _PTJDD.Bits.PTJDD5
#define PTJDD_PTJDD6                    _PTJDD.Bits.PTJDD6
#define PTJDD_PTJDD7                    _PTJDD.Bits.PTJDD7

#define PTJDD_PTJDD0_MASK               1U
#define PTJDD_PTJDD1_MASK               2U
#define PTJDD_PTJDD2_MASK               4U
#define PTJDD_PTJDD3_MASK               8U
#define PTJDD_PTJDD4_MASK               16U
#define PTJDD_PTJDD5_MASK               32U
#define PTJDD_PTJDD6_MASK               64U
#define PTJDD_PTJDD7_MASK               128U


/*** IIC1A - IIC Address Register; 0x00000030 ***/
typedef union {
  byte Byte;
  struct {
    byte             :1; 
    byte AD1         :1;                                       /* Slave Address Bit 1 */
    byte AD2         :1;                                       /* Slave Address Bit 2 */
    byte AD3         :1;                                       /* Slave Address Bit 3 */
    byte AD4         :1;                                       /* Slave Address Bit 4 */
    byte AD5         :1;                                       /* Slave Address Bit 5 */
    byte AD6         :1;                                       /* Slave Address Bit 6 */
    byte AD7         :1;                                       /* Slave Address Bit 7 */
  } Bits;
  struct {
    byte         :1;
    byte grpAD_1 :7;
  } MergedBits;
} IIC1ASTR;
extern volatile IIC1ASTR _IIC1A @0x00000030;
#define IIC1A                           _IIC1A.Byte
#define IIC1A_AD1                       _IIC1A.Bits.AD1
#define IIC1A_AD2                       _IIC1A.Bits.AD2
#define IIC1A_AD3                       _IIC1A.Bits.AD3
#define IIC1A_AD4                       _IIC1A.Bits.AD4
#define IIC1A_AD5                       _IIC1A.Bits.AD5
#define IIC1A_AD6                       _IIC1A.Bits.AD6
#define IIC1A_AD7                       _IIC1A.Bits.AD7
#define IIC1A_AD_1                      _IIC1A.MergedBits.grpAD_1
#define IIC1A_AD                        IIC1A_AD_1

#define IIC1A_AD1_MASK                  2U
#define IIC1A_AD2_MASK                  4U
#define IIC1A_AD3_MASK                  8U
#define IIC1A_AD4_MASK                  16U
#define IIC1A_AD5_MASK                  32U
#define IIC1A_AD6_MASK                  64U
#define IIC1A_AD7_MASK                  128U
#define IIC1A_AD_1_MASK                 254U
#define IIC1A_AD_1_BITNUM               1U


/*** IIC1F - IIC Frequency Divider Register; 0x00000031 ***/
typedef union {
  byte Byte;
  struct {
    byte ICR0        :1;                                       /* IIC Clock Rate Bit 0 */
    byte ICR1        :1;                                       /* IIC Clock Rate Bit 1 */
    byte ICR2        :1;                                       /* IIC Clock Rate Bit 2 */
    byte ICR3        :1;                                       /* IIC Clock Rate Bit 3 */
    byte ICR4        :1;                                       /* IIC Clock Rate Bit 4 */
    byte ICR5        :1;                                       /* IIC Clock Rate Bit 5 */
    byte MULT0       :1;                                       /* Multiplier Factor Bit 0 */
    byte MULT1       :1;                                       /* Multiplier Factor Bit 1 */
  } Bits;
  struct {
    byte grpICR  :6;
    byte grpMULT :2;
  } MergedBits;
} IIC1FSTR;
extern volatile IIC1FSTR _IIC1F @0x00000031;
#define IIC1F                           _IIC1F.Byte
#define IIC1F_ICR0                      _IIC1F.Bits.ICR0
#define IIC1F_ICR1                      _IIC1F.Bits.ICR1
#define IIC1F_ICR2                      _IIC1F.Bits.ICR2
#define IIC1F_ICR3                      _IIC1F.Bits.ICR3
#define IIC1F_ICR4                      _IIC1F.Bits.ICR4
#define IIC1F_ICR5                      _IIC1F.Bits.ICR5
#define IIC1F_MULT0                     _IIC1F.Bits.MULT0
#define IIC1F_MULT1                     _IIC1F.Bits.MULT1
#define IIC1F_ICR                       _IIC1F.MergedBits.grpICR
#define IIC1F_MULT                      _IIC1F.MergedBits.grpMULT

#define IIC1F_ICR0_MASK                 1U
#define IIC1F_ICR1_MASK                 2U
#define IIC1F_ICR2_MASK                 4U
#define IIC1F_ICR3_MASK                 8U
#define IIC1F_ICR4_MASK                 16U
#define IIC1F_ICR5_MASK                 32U
#define IIC1F_MULT0_MASK                64U
#define IIC1F_MULT1_MASK                128U
#define IIC1F_ICR_MASK                  63U
#define IIC1F_ICR_BITNUM                0U
#define IIC1F_MULT_MASK                 192U
#define IIC1F_MULT_BITNUM               6U


/*** IIC1C1 - IIC Control Register 1; 0x00000032 ***/
typedef union {
  byte Byte;
  union { /* Several registers at the same address */
    /*** IIC1C1 - IIC Control Register 1; Several registers at the same address ***/
    union {
      struct {
        byte             :1; 
        byte             :1; 
        byte RSTA        :1;                                       /* Repeat START */
        byte TXAK        :1;                                       /* Transmit Acknowledge Enable */
        byte TX          :1;                                       /* Transmit Mode Select */
        byte MST         :1;                                       /* Master Mode Select */
        byte IICIE       :1;                                       /* IIC Interrupt Enable */
        byte IICEN       :1;                                       /* IIC Enable */
      } Bits;
    } IIC1C1STR;
    #define IIC1C1                      _IIC1C1.Byte
    #define IIC1C1_RSTA                 _IIC1C1.SameAddr_STR.IIC1C1STR.Bits.RSTA
    #define IIC1C1_TXAK                 _IIC1C1.SameAddr_STR.IIC1C1STR.Bits.TXAK
    #define IIC1C1_TX                   _IIC1C1.SameAddr_STR.IIC1C1STR.Bits.TX
    #define IIC1C1_MST                  _IIC1C1.SameAddr_STR.IIC1C1STR.Bits.MST
    #define IIC1C1_IICIE                _IIC1C1.SameAddr_STR.IIC1C1STR.Bits.IICIE
    #define IIC1C1_IICEN                _IIC1C1.SameAddr_STR.IIC1C1STR.Bits.IICEN
    
    #define IIC1C1_RSTA_MASK            4U
    #define IIC1C1_TXAK_MASK            8U
    #define IIC1C1_TX_MASK              16U
    #define IIC1C1_MST_MASK             32U
    #define IIC1C1_IICIE_MASK           64U
    #define IIC1C1_IICEN_MASK           128U
    
    /*** IIC1C - IIC Control Register; Several registers at the same address ***/
    union {
      struct {
        byte             :1; 
        byte             :1; 
        byte RSTA        :1;                                       /* Repeat START */
        byte TXAK        :1;                                       /* Transmit Acknowledge Enable */
        byte TX          :1;                                       /* Transmit Mode Select */
        byte MST         :1;                                       /* Master Mode Select */
        byte IICIE       :1;                                       /* IIC Interrupt Enable */
        byte IICEN       :1;                                       /* IIC Enable */
      } Bits;
    } IIC1CSTR;
    #define IIC1C                       _IIC1C1.Byte
    #define IIC1C_RSTA                  _IIC1C1.SameAddr_STR.IIC1CSTR.Bits.RSTA
    #define IIC1C_TXAK                  _IIC1C1.SameAddr_STR.IIC1CSTR.Bits.TXAK
    #define IIC1C_TX                    _IIC1C1.SameAddr_STR.IIC1CSTR.Bits.TX
    #define IIC1C_MST                   _IIC1C1.SameAddr_STR.IIC1CSTR.Bits.MST
    #define IIC1C_IICIE                 _IIC1C1.SameAddr_STR.IIC1CSTR.Bits.IICIE
    #define IIC1C_IICEN                 _IIC1C1.SameAddr_STR.IIC1CSTR.Bits.IICEN
    
    #define IIC1C_RSTA_MASK             4U
    #define IIC1C_TXAK_MASK             8U
    #define IIC1C_TX_MASK               16U
    #define IIC1C_MST_MASK              32U
    #define IIC1C_IICIE_MASK            64U
    #define IIC1C_IICEN_MASK            128U
    
  } SameAddr_STR; /*Several registers at the same address */

} IIC1C1STR;
extern volatile IIC1C1STR _IIC1C1 @0x00000032;


/*** IIC1S - IIC Status Register; 0x00000033 ***/
typedef union {
  byte Byte;
  struct {
    byte RXAK        :1;                                       /* Receive Acknowledge */
    byte IICIF       :1;                                       /* IIC Interrupt Flag */
    byte SRW         :1;                                       /* Slave Read/Write */
    byte             :1; 
    byte ARBL        :1;                                       /* Arbitration Lost */
    byte BUSY        :1;                                       /* Bus Busy */
    byte IAAS        :1;                                       /* Addressed as a Slave */
    byte TCF         :1;                                       /* Transfer Complete Flag */
  } Bits;
} IIC1SSTR;
extern volatile IIC1SSTR _IIC1S @0x00000033;
#define IIC1S                           _IIC1S.Byte
#define IIC1S_RXAK                      _IIC1S.Bits.RXAK
#define IIC1S_IICIF                     _IIC1S.Bits.IICIF
#define IIC1S_SRW                       _IIC1S.Bits.SRW
#define IIC1S_ARBL                      _IIC1S.Bits.ARBL
#define IIC1S_BUSY                      _IIC1S.Bits.BUSY
#define IIC1S_IAAS                      _IIC1S.Bits.IAAS
#define IIC1S_TCF                       _IIC1S.Bits.TCF

#define IIC1S_RXAK_MASK                 1U
#define IIC1S_IICIF_MASK                2U
#define IIC1S_SRW_MASK                  4U
#define IIC1S_ARBL_MASK                 16U
#define IIC1S_BUSY_MASK                 32U
#define IIC1S_IAAS_MASK                 64U
#define IIC1S_TCF_MASK                  128U


/*** IIC1D - IIC Data I/O Register; 0x00000034 ***/
typedef union {
  byte Byte;
  struct {
    byte DATA0       :1;                                       /* IIC Data Bit 0 */
    byte DATA1       :1;                                       /* IIC Data Bit 1 */
    byte DATA2       :1;                                       /* IIC Data Bit 2 */
    byte DATA3       :1;                                       /* IIC Data Bit 3 */
    byte DATA4       :1;                                       /* IIC Data Bit 4 */
    byte DATA5       :1;                                       /* IIC Data Bit 5 */
    byte DATA6       :1;                                       /* IIC Data Bit 6 */
    byte DATA7       :1;                                       /* IIC Data Bit 7 */
  } Bits;
} IIC1DSTR;
extern volatile IIC1DSTR _IIC1D @0x00000034;
#define IIC1D                           _IIC1D.Byte
#define IIC1D_DATA0                     _IIC1D.Bits.DATA0
#define IIC1D_DATA1                     _IIC1D.Bits.DATA1
#define IIC1D_DATA2                     _IIC1D.Bits.DATA2
#define IIC1D_DATA3                     _IIC1D.Bits.DATA3
#define IIC1D_DATA4                     _IIC1D.Bits.DATA4
#define IIC1D_DATA5                     _IIC1D.Bits.DATA5
#define IIC1D_DATA6                     _IIC1D.Bits.DATA6
#define IIC1D_DATA7                     _IIC1D.Bits.DATA7

#define IIC1D_DATA0_MASK                1U
#define IIC1D_DATA1_MASK                2U
#define IIC1D_DATA2_MASK                4U
#define IIC1D_DATA3_MASK                8U
#define IIC1D_DATA4_MASK                16U
#define IIC1D_DATA5_MASK                32U
#define IIC1D_DATA6_MASK                64U
#define IIC1D_DATA7_MASK                128U


/*** IIC1C2 - IIC Control Register 2; 0x00000035 ***/
typedef union {
  byte Byte;
  struct {
    byte AD8         :1;                                       /* Slave Address Bit 8 */
    byte AD9         :1;                                       /* Slave Address Bit 9 */
    byte AD10        :1;                                       /* Slave Address Bit 10 */
    byte             :1; 
    byte             :1; 
    byte             :1; 
    byte ADEXT       :1;                                       /* Address Extension */
    byte GCAEN       :1;                                       /* General Call Address Enable */
  } Bits;
  struct {
    byte grpAD_8 :3;
    byte         :1;
    byte         :1;
    byte         :1;
    byte         :1;
    byte         :1;
  } MergedBits;
} IIC1C2STR;
extern volatile IIC1C2STR _IIC1C2 @0x00000035;
#define IIC1C2                          _IIC1C2.Byte
#define IIC1C2_AD8                      _IIC1C2.Bits.AD8
#define IIC1C2_AD9                      _IIC1C2.Bits.AD9
#define IIC1C2_AD10                     _IIC1C2.Bits.AD10
#define IIC1C2_ADEXT                    _IIC1C2.Bits.ADEXT
#define IIC1C2_GCAEN                    _IIC1C2.Bits.GCAEN
#define IIC1C2_AD_8                     _IIC1C2.MergedBits.grpAD_8
#define IIC1C2_AD                       IIC1C2_AD_8

#define IIC1C2_AD8_MASK                 1U
#define IIC1C2_AD9_MASK                 2U
#define IIC1C2_AD10_MASK                4U
#define IIC1C2_ADEXT_MASK               64U
#define IIC1C2_GCAEN_MASK               128U
#define IIC1C2_AD_8_MASK                7U
#define IIC1C2_AD_8_BITNUM              0U


/*** ICSC1 - ICS Control Register 1; 0x00000038 ***/
typedef union {
  byte Byte;
  struct {
    byte IREFSTEN    :1;                                       /* Internal Reference Stop Enable */
    byte IRCLKEN     :1;                                       /* Internal Reference Clock Enable */
    byte IREFS       :1;                                       /* Internal Reference Select */
    byte RDIV0       :1;                                       /* Reference Divider, bit 0 */
    byte RDIV1       :1;                                       /* Reference Divider, bit 1 */
    byte RDIV2       :1;                                       /* Reference Divider, bit 2 */
    byte CLKS0       :1;                                       /* Clock Source Select, bit 0 */
    byte CLKS1       :1;                                       /* Clock Source Select, bit 1 */
  } Bits;
  struct {
    byte         :1;
    byte         :1;
    byte         :1;
    byte grpRDIV :3;
    byte grpCLKS :2;
  } MergedBits;
} ICSC1STR;
extern volatile ICSC1STR _ICSC1 @0x00000038;
#define ICSC1                           _ICSC1.Byte
#define ICSC1_IREFSTEN                  _ICSC1.Bits.IREFSTEN
#define ICSC1_IRCLKEN                   _ICSC1.Bits.IRCLKEN
#define ICSC1_IREFS                     _ICSC1.Bits.IREFS
#define ICSC1_RDIV0                     _ICSC1.Bits.RDIV0
#define ICSC1_RDIV1                     _ICSC1.Bits.RDIV1
#define ICSC1_RDIV2                     _ICSC1.Bits.RDIV2
#define ICSC1_CLKS0                     _ICSC1.Bits.CLKS0
#define ICSC1_CLKS1                     _ICSC1.Bits.CLKS1
#define ICSC1_RDIV                      _ICSC1.MergedBits.grpRDIV
#define ICSC1_CLKS                      _ICSC1.MergedBits.grpCLKS

#define ICSC1_IREFSTEN_MASK             1U
#define ICSC1_IRCLKEN_MASK              2U
#define ICSC1_IREFS_MASK                4U
#define ICSC1_RDIV0_MASK                8U
#define ICSC1_RDIV1_MASK                16U
#define ICSC1_RDIV2_MASK                32U
#define ICSC1_CLKS0_MASK                64U
#define ICSC1_CLKS1_MASK                128U
#define ICSC1_RDIV_MASK                 56U
#define ICSC1_RDIV_BITNUM               3U
#define ICSC1_CLKS_MASK                 192U
#define ICSC1_CLKS_BITNUM               6U


/*** ICSC2 - ICS Control Register 2; 0x00000039 ***/
typedef union {
  byte Byte;
  struct {
    byte EREFSTEN    :1;                                       /* External Reference Stop Enable */
    byte ERCLKEN     :1;                                       /* External Reference Enable */
    byte EREFS       :1;                                       /* External Reference Select */
    byte LP          :1;                                       /* Low Power Select */
    byte HGO         :1;                                       /* High Gain Oscillator Select */
    byte RANGE       :1;                                       /* Frequency Range Select */
    byte BDIV0       :1;                                       /* Bus Frequency Divider, bit 0 */
    byte BDIV1       :1;                                       /* Bus Frequency Divider, bit 1 */
  } Bits;
  struct {
    byte         :1;
    byte         :1;
    byte         :1;
    byte         :1;
    byte         :1;
    byte         :1;
    byte grpBDIV :2;
  } MergedBits;
} ICSC2STR;
extern volatile ICSC2STR _ICSC2 @0x00000039;
#define ICSC2                           _ICSC2.Byte
#define ICSC2_EREFSTEN                  _ICSC2.Bits.EREFSTEN
#define ICSC2_ERCLKEN                   _ICSC2.Bits.ERCLKEN
#define ICSC2_EREFS                     _ICSC2.Bits.EREFS
#define ICSC2_LP                        _ICSC2.Bits.LP
#define ICSC2_HGO                       _ICSC2.Bits.HGO
#define ICSC2_RANGE                     _ICSC2.Bits.RANGE
#define ICSC2_BDIV0                     _ICSC2.Bits.BDIV0
#define ICSC2_BDIV1                     _ICSC2.Bits.BDIV1
#define ICSC2_BDIV                      _ICSC2.MergedBits.grpBDIV

#define ICSC2_EREFSTEN_MASK             1U
#define ICSC2_ERCLKEN_MASK              2U
#define ICSC2_EREFS_MASK                4U
#define ICSC2_LP_MASK                   8U
#define ICSC2_HGO_MASK                  16U
#define ICSC2_RANGE_MASK                32U
#define ICSC2_BDIV0_MASK                64U
#define ICSC2_BDIV1_MASK                128U
#define ICSC2_BDIV_MASK                 192U
#define ICSC2_BDIV_BITNUM               6U


/*** ICSTRM - ICS Trim Register; 0x0000003A ***/
typedef union {
  byte Byte;
  struct {
    byte TRIM0       :1;                                       /* ICS Trim Setting, bit 0 */
    byte TRIM1       :1;                                       /* ICS Trim Setting, bit 1 */
    byte TRIM2       :1;                                       /* ICS Trim Setting, bit 2 */
    byte TRIM3       :1;                                       /* ICS Trim Setting, bit 3 */
    byte TRIM4       :1;                                       /* ICS Trim Setting, bit 4 */
    byte TRIM5       :1;                                       /* ICS Trim Setting, bit 5 */
    byte TRIM6       :1;                                       /* ICS Trim Setting, bit 6 */
    byte TRIM7       :1;                                       /* ICS Trim Setting, bit 7 */
  } Bits;
} ICSTRMSTR;
extern volatile ICSTRMSTR _ICSTRM @0x0000003A;
#define ICSTRM                          _ICSTRM.Byte
#define ICSTRM_TRIM0                    _ICSTRM.Bits.TRIM0
#define ICSTRM_TRIM1                    _ICSTRM.Bits.TRIM1
#define ICSTRM_TRIM2                    _ICSTRM.Bits.TRIM2
#define ICSTRM_TRIM3                    _ICSTRM.Bits.TRIM3
#define ICSTRM_TRIM4                    _ICSTRM.Bits.TRIM4
#define ICSTRM_TRIM5                    _ICSTRM.Bits.TRIM5
#define ICSTRM_TRIM6                    _ICSTRM.Bits.TRIM6
#define ICSTRM_TRIM7                    _ICSTRM.Bits.TRIM7

#define ICSTRM_TRIM0_MASK               1U
#define ICSTRM_TRIM1_MASK               2U
#define ICSTRM_TRIM2_MASK               4U
#define ICSTRM_TRIM3_MASK               8U
#define ICSTRM_TRIM4_MASK               16U
#define ICSTRM_TRIM5_MASK               32U
#define ICSTRM_TRIM6_MASK               64U
#define ICSTRM_TRIM7_MASK               128U


/*** ICSSC - ICS Status and Control Register; 0x0000003B ***/
typedef union {
  byte Byte;
  struct {
    byte FTRIM       :1;                                       /* ICS Fine Trim */
    byte OSCINIT     :1;                                       /* OSC Initialization */
    byte CLKST0      :1;                                       /* Clock Mode Status, bit 0 */
    byte CLKST1      :1;                                       /* Clock Mode Status, bit 1 */
    byte IREFST      :1;                                       /* Internal Reference Status */
    byte DMX32       :1;                                       /* DCO Maximum frequency with 32.768 kHz reference */
    byte DRST_DRS0   :1;                                       /* DCO Range Status/Range Select, bit 0 */
    byte DRST_DRS1   :1;                                       /* DCO Range Status/Range Select, bit 1 */
  } Bits;
  struct {
    byte         :1;
    byte         :1;
    byte grpCLKST :2;
    byte         :1;
    byte grpDMX_32 :1;
    byte grpDRST_DRS :2;
  } MergedBits;
} ICSSCSTR;
extern volatile ICSSCSTR _ICSSC @0x0000003B;
#define ICSSC                           _ICSSC.Byte
#define ICSSC_FTRIM                     _ICSSC.Bits.FTRIM
#define ICSSC_OSCINIT                   _ICSSC.Bits.OSCINIT
#define ICSSC_CLKST0                    _ICSSC.Bits.CLKST0
#define ICSSC_CLKST1                    _ICSSC.Bits.CLKST1
#define ICSSC_IREFST                    _ICSSC.Bits.IREFST
#define ICSSC_DMX32                     _ICSSC.Bits.DMX32
#define ICSSC_DRST_DRS0                 _ICSSC.Bits.DRST_DRS0
#define ICSSC_DRST_DRS1                 _ICSSC.Bits.DRST_DRS1
#define ICSSC_CLKST                     _ICSSC.MergedBits.grpCLKST
#define ICSSC_DRST_DRS                  _ICSSC.MergedBits.grpDRST_DRS

#define ICSSC_FTRIM_MASK                1U
#define ICSSC_OSCINIT_MASK              2U
#define ICSSC_CLKST0_MASK               4U
#define ICSSC_CLKST1_MASK               8U
#define ICSSC_IREFST_MASK               16U
#define ICSSC_DMX32_MASK                32U
#define ICSSC_DRST_DRS0_MASK            64U
#define ICSSC_DRST_DRS1_MASK            128U
#define ICSSC_CLKST_MASK                12U
#define ICSSC_CLKST_BITNUM              2U
#define ICSSC_DRST_DRS_MASK             192U
#define ICSSC_DRST_DRS_BITNUM           6U


/*** KBI2SC - KBI2 Status and Control Register; 0x0000003C ***/
typedef union {
  byte Byte;
  struct {
    byte KBIMOD      :1;                                       /* Keyboard Detection Mode */
    byte KBIE        :1;                                       /* Keyboard Interrupt Enable */
    byte KBACK       :1;                                       /* Keyboard Interrupt Acknowledge */
    byte KBF         :1;                                       /* Keyboard Interrupt Flag */
    byte             :1; 
    byte             :1; 
    byte             :1; 
    byte             :1; 
  } Bits;
} KBI2SCSTR;
extern volatile KBI2SCSTR _KBI2SC @0x0000003C;
#define KBI2SC                          _KBI2SC.Byte
#define KBI2SC_KBIMOD                   _KBI2SC.Bits.KBIMOD
#define KBI2SC_KBIE                     _KBI2SC.Bits.KBIE
#define KBI2SC_KBACK                    _KBI2SC.Bits.KBACK
#define KBI2SC_KBF                      _KBI2SC.Bits.KBF

#define KBI2SC_KBIMOD_MASK              1U
#define KBI2SC_KBIE_MASK                2U
#define KBI2SC_KBACK_MASK               4U
#define KBI2SC_KBF_MASK                 8U


/*** KBI2PE - KBI2 Pin Enable Register; 0x0000003D ***/
typedef union {
  byte Byte;
  struct {
    byte KBIPE0      :1;                                       /* Keyboard Pin Enable for KBI Port Bit 0 */
    byte KBIPE1      :1;                                       /* Keyboard Pin Enable for KBI Port Bit 1 */
    byte KBIPE2      :1;                                       /* Keyboard Pin Enable for KBI Port Bit 2 */
    byte KBIPE3      :1;                                       /* Keyboard Pin Enable for KBI Port Bit 3 */
    byte KBIPE4      :1;                                       /* Keyboard Pin Enable for KBI Port Bit 4 */
    byte KBIPE5      :1;                                       /* Keyboard Pin Enable for KBI Port Bit 5 */
    byte KBIPE6      :1;                                       /* Keyboard Pin Enable for KBI Port Bit 6 */
    byte KBIPE7      :1;                                       /* Keyboard Pin Enable for KBI Port Bit 7 */
  } Bits;
} KBI2PESTR;
extern volatile KBI2PESTR _KBI2PE @0x0000003D;
#define KBI2PE                          _KBI2PE.Byte
#define KBI2PE_KBIPE0                   _KBI2PE.Bits.KBIPE0
#define KBI2PE_KBIPE1                   _KBI2PE.Bits.KBIPE1
#define KBI2PE_KBIPE2                   _KBI2PE.Bits.KBIPE2
#define KBI2PE_KBIPE3                   _KBI2PE.Bits.KBIPE3
#define KBI2PE_KBIPE4                   _KBI2PE.Bits.KBIPE4
#define KBI2PE_KBIPE5                   _KBI2PE.Bits.KBIPE5
#define KBI2PE_KBIPE6                   _KBI2PE.Bits.KBIPE6
#define KBI2PE_KBIPE7                   _KBI2PE.Bits.KBIPE7

#define KBI2PE_KBIPE0_MASK              1U
#define KBI2PE_KBIPE1_MASK              2U
#define KBI2PE_KBIPE2_MASK              4U
#define KBI2PE_KBIPE3_MASK              8U
#define KBI2PE_KBIPE4_MASK              16U
#define KBI2PE_KBIPE5_MASK              32U
#define KBI2PE_KBIPE6_MASK              64U
#define KBI2PE_KBIPE7_MASK              128U


/*** KBI2ES - KBI2 Edge Select Register; 0x0000003E ***/
typedef union {
  byte Byte;
  struct {
    byte KBEDG0      :1;                                       /* Keyboard Edge Select Bit 0 */
    byte KBEDG1      :1;                                       /* Keyboard Edge Select Bit 1 */
    byte KBEDG2      :1;                                       /* Keyboard Edge Select Bit 2 */
    byte KBEDG3      :1;                                       /* Keyboard Edge Select Bit 3 */
    byte KBEDG4      :1;                                       /* Keyboard Edge Select Bit 4 */
    byte KBEDG5      :1;                                       /* Keyboard Edge Select Bit 5 */
    byte KBEDG6      :1;                                       /* Keyboard Edge Select Bit 6 */
    byte KBEDG7      :1;                                       /* Keyboard Edge Select Bit 7 */
  } Bits;
} KBI2ESSTR;
extern volatile KBI2ESSTR _KBI2ES @0x0000003E;
#define KBI2ES                          _KBI2ES.Byte
#define KBI2ES_KBEDG0                   _KBI2ES.Bits.KBEDG0
#define KBI2ES_KBEDG1                   _KBI2ES.Bits.KBEDG1
#define KBI2ES_KBEDG2                   _KBI2ES.Bits.KBEDG2
#define KBI2ES_KBEDG3                   _KBI2ES.Bits.KBEDG3
#define KBI2ES_KBEDG4                   _KBI2ES.Bits.KBEDG4
#define KBI2ES_KBEDG5                   _KBI2ES.Bits.KBEDG5
#define KBI2ES_KBEDG6                   _KBI2ES.Bits.KBEDG6
#define KBI2ES_KBEDG7                   _KBI2ES.Bits.KBEDG7

#define KBI2ES_KBEDG0_MASK              1U
#define KBI2ES_KBEDG1_MASK              2U
#define KBI2ES_KBEDG2_MASK              4U
#define KBI2ES_KBEDG3_MASK              8U
#define KBI2ES_KBEDG4_MASK              16U
#define KBI2ES_KBEDG5_MASK              32U
#define KBI2ES_KBEDG6_MASK              64U
#define KBI2ES_KBEDG7_MASK              128U


/*** TPM1SC - TPM1 Status and Control Register; 0x00000040 ***/
typedef union {
  byte Byte;
  struct {
    byte PS0         :1;                                       /* Prescale Divisor Select Bit 0 */
    byte PS1         :1;                                       /* Prescale Divisor Select Bit 1 */
    byte PS2         :1;                                       /* Prescale Divisor Select Bit 2 */
    byte CLKSA       :1;                                       /* Clock Source Select A */
    byte CLKSB       :1;                                       /* Clock Source Select B */
    byte CPWMS       :1;                                       /* Center-Aligned PWM Select */
    byte TOIE        :1;                                       /* Timer Overflow Interrupt Enable */
    byte TOF         :1;                                       /* Timer Overflow Flag */
  } Bits;
  struct {
    byte grpPS   :3;
    byte grpCLKSx :2;
    byte         :1;
    byte         :1;
    byte         :1;
  } MergedBits;
} TPM1SCSTR;
extern volatile TPM1SCSTR _TPM1SC @0x00000040;
#define TPM1SC                          _TPM1SC.Byte
#define TPM1SC_PS0                      _TPM1SC.Bits.PS0
#define TPM1SC_PS1                      _TPM1SC.Bits.PS1
#define TPM1SC_PS2                      _TPM1SC.Bits.PS2
#define TPM1SC_CLKSA                    _TPM1SC.Bits.CLKSA
#define TPM1SC_CLKSB                    _TPM1SC.Bits.CLKSB
#define TPM1SC_CPWMS                    _TPM1SC.Bits.CPWMS
#define TPM1SC_TOIE                     _TPM1SC.Bits.TOIE
#define TPM1SC_TOF                      _TPM1SC.Bits.TOF
#define TPM1SC_PS                       _TPM1SC.MergedBits.grpPS
#define TPM1SC_CLKSx                    _TPM1SC.MergedBits.grpCLKSx
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
