exsilium/pxbee-trigger/pxbee/headers/xbee/discovery.h

/*
 * Copyright (c) 2011-2012 Digi International Inc.,
 * All rights not expressly granted are reserved.
 *
 * This Source Code Form is subject to the terms of the Mozilla Public
 * License, v. 2.0. If a copy of the MPL was not distributed with this file,
 * You can obtain one at http://mozilla.org/MPL/2.0/.
 *
 * Digi International Inc. 11001 Bren Road East, Minnetonka, MN 55343
 * =======================================================================
 */

/**
	@addtogroup xbee_discovery
	@{
	@file xbee/discovery.h
	Header for code related to "Node Discovery" (the ATND command, 0x95 frames)

	Note that Node Discovery isn't supported on XBee Smart Energy firmware.

	A host can initiate Node Discovery by sending an ATND command to its local
	XBee.  The command can include a parameter of the NI string of a single
	node on the network to discover.  See the xbee_disc_discover_nodes() API
	for sending this request.

	Responses come in as AT Command Response frames (type 0x88) containing a
	Node ID message.

	Additionally, nodes on a network will broadcast unsolicited (i.e., not in
	response to an ATND command) Node ID messages to the rest of the network
	in two instances:

		1) The device has ATJN set to 1, and it has just joined the network.

		2) The user has configured D0 as the commissioning button, and presses
			the commissioning button once.

	The receiving node will pass the message on to the host in one of two ways:

		1) If AO is set to 0, the host receives a Node ID frame (type 0x95).

		2) If AO is non-zero, the host receives an Explicit Rx frame (type 0x91)
			for the Node ID Message cluster (0x0095) of the Digi Data endpoint
			(0xE8).

	This library provides an API layer for handling these responses.  The host
	needs to follow these steps to receive NODE ID messages.

		1) Write a function to receive the messages, with the following signature:
				void node_discovered( xbee_dev_t *xbee, const xbee_node_id_t *rec)

		2) Register that function at startup to receive messages:
				xbee_disc_add_node_id_handler( &my_xbee, &node_discovered);

		3) Include the ATND Response handler in the xbee_frame_handlers table
			using the macro XBEE_FRAME_HANDLE_ATND_RESPONSE.

		4) If using a module with ATAO set to 0, include the Node ID handler
			in the xbee_frame_handlers table using the macro
			XBEE_FRAME_HANDLE_AO0_NODEID.

		5) If using a module with ATAO set to 1 or 3, include the Node ID Cluster
			handler in the Digi Data endpoint's cluster table, using the
			XBEE_DISC_DIGI_DATA_CLUSTER_ENTRY macro, and include the Explicit RX
			handler in the xbee_frame_handlers table using the macro
			XBEE_FRAME_HANDLE_RX_EXPLICIT.
*/

#ifndef XBEE_DISCOVERY_H
#define XBEE_DISCOVERY_H

#include "xbee/platform.h"
#include "xbee/device.h"
#include "wpan/types.h"

XBEE_BEGIN_DECLS

/// Maximum length of a Node ID string (ATNI value) (excludes null terminator).
#define XBEE_DISC_MAX_NODEID_LEN 20

typedef PACKED_STRUCT xbee_node_id1_t {
	uint16_t			network_addr_be;		///< ATMY value [0xFFFE on DigiMesh]
	addr64			ieee_addr_be;			///< ATSH and ATSL
	/// null-terminated ATNI value (variable length)
	char				node_info[XBEE_DISC_MAX_NODEID_LEN + 1];
} xbee_node_id1_t;

// data following variable-length node info
typedef PACKED_STRUCT xbee_node_id2_t {
	uint16_t			parent_addr_be;		///< ATMP value [0xFFFE on DigiMesh]

	uint8_t			device_type;			///< one of XBEE_ND_DEVICE_* macro values
		#define XBEE_ND_DEVICE_TYPE_COORD	0
		#define XBEE_ND_DEVICE_TYPE_ROUTER	1
		#define XBEE_ND_DEVICE_TYPE_ENDDEV	2

	uint8_t			source_event;			///< event that generated the ND frame
		#define XBEE_ND_SOURCE_EVENT_NONE			0
		#define XBEE_ND_SOURCE_EVENT_PUSHBUTTON	1
		#define XBEE_ND_SOURCE_EVENT_JOINED			2
		#define XBEE_ND_SOURCE_EVENT_POWER_CYCLE	3

	uint16_t			profile_be;				///< Digi Profile ID (0xC105)
	uint16_t			manufacturer_be;		///< Manufacturer ID (0x101E)

	/// ATDD of remote device [optional field enabled with ATNO on DigiMesh]
	uint32_t			device_id_be;

	/// RSSI of packet [optional field enabled with ATNO on DigiMesh]
	uint8_t			rssi;
} xbee_node_id2_t;
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
